bytendomods/RLCD-DMG/journey/img/IMG_0250 Large.jpeg

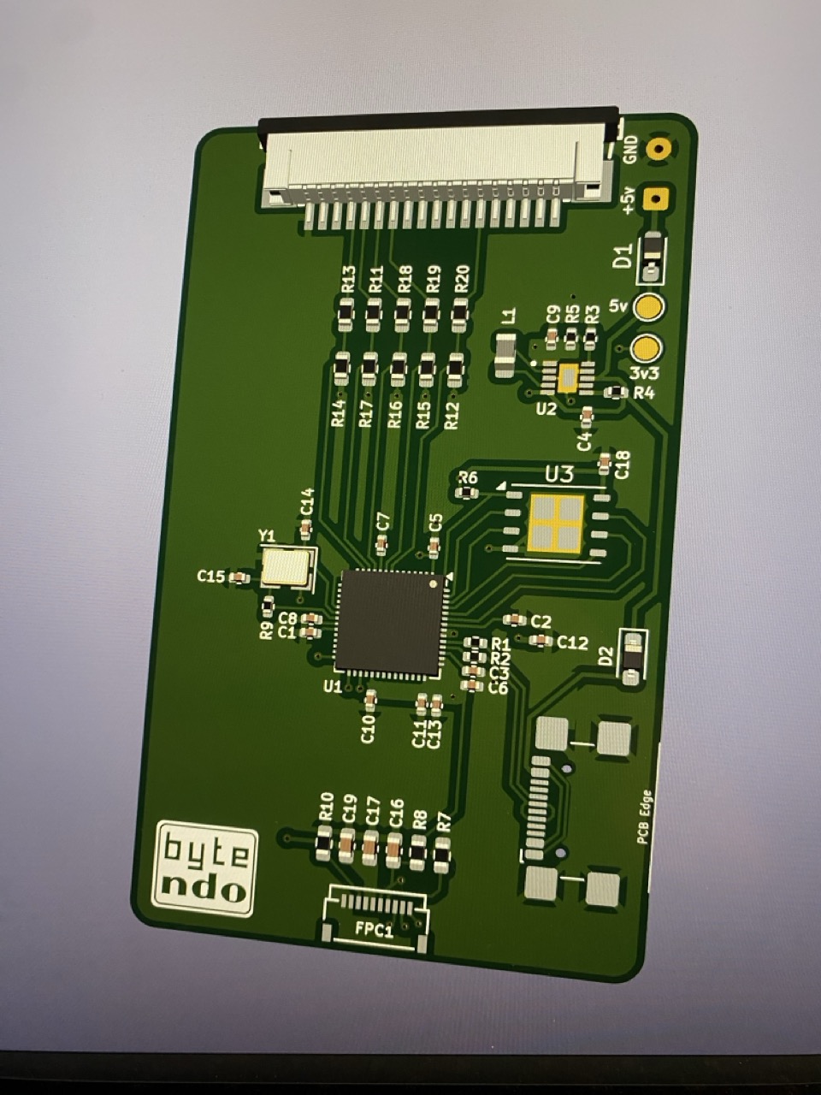
journey/img/IMG_0250 Large.jpeg
