bytendomods/RLCD-DMG/journey/img/IMG_0370 Large.jpeg

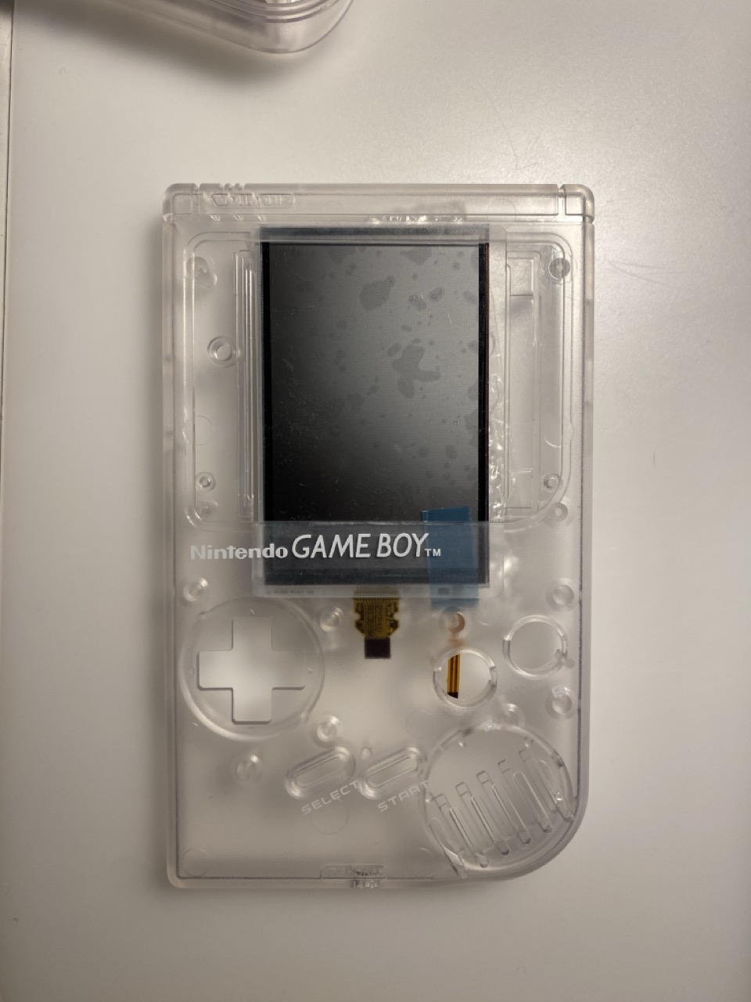
journey/img/IMG_0370 Large.jpeg
