bytendomods/RLCD-DMG/journey/img/IMG_0482 Large.jpeg

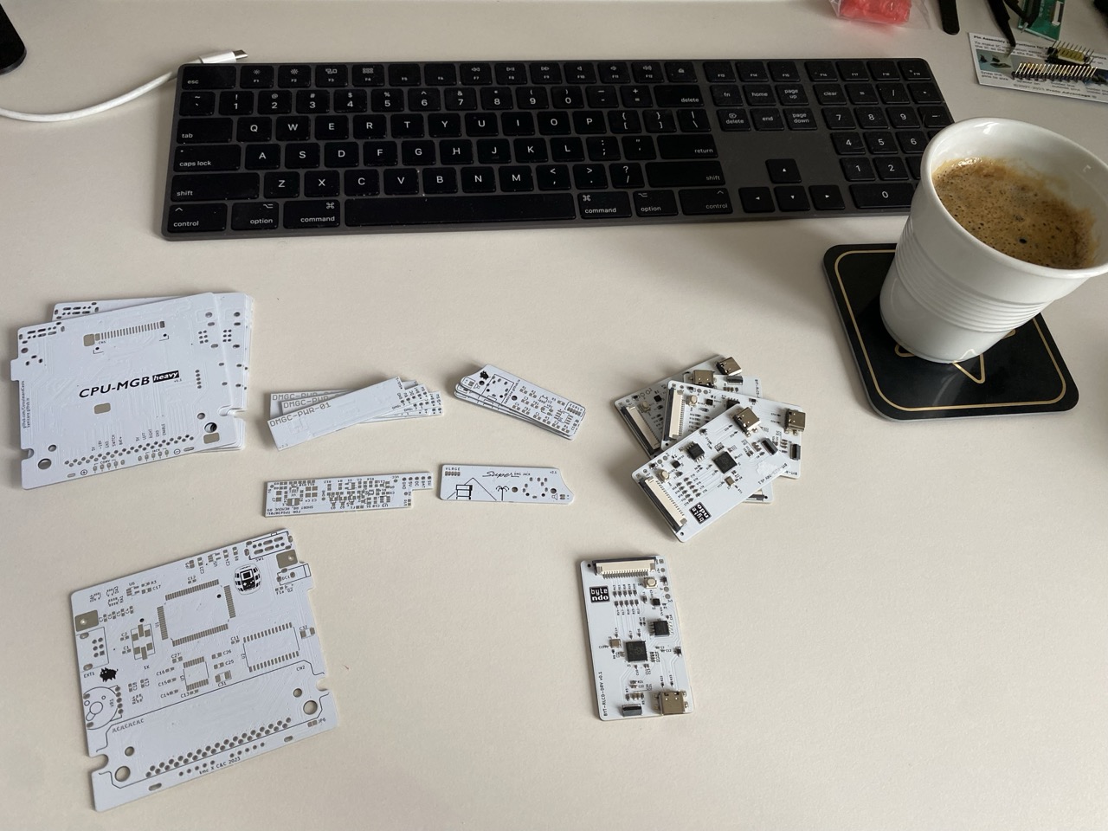
journey/img/IMG_0482 Large.jpeg
