bytendomods/RLCD-DMG/journey/img/IMG_0483 Large.jpeg

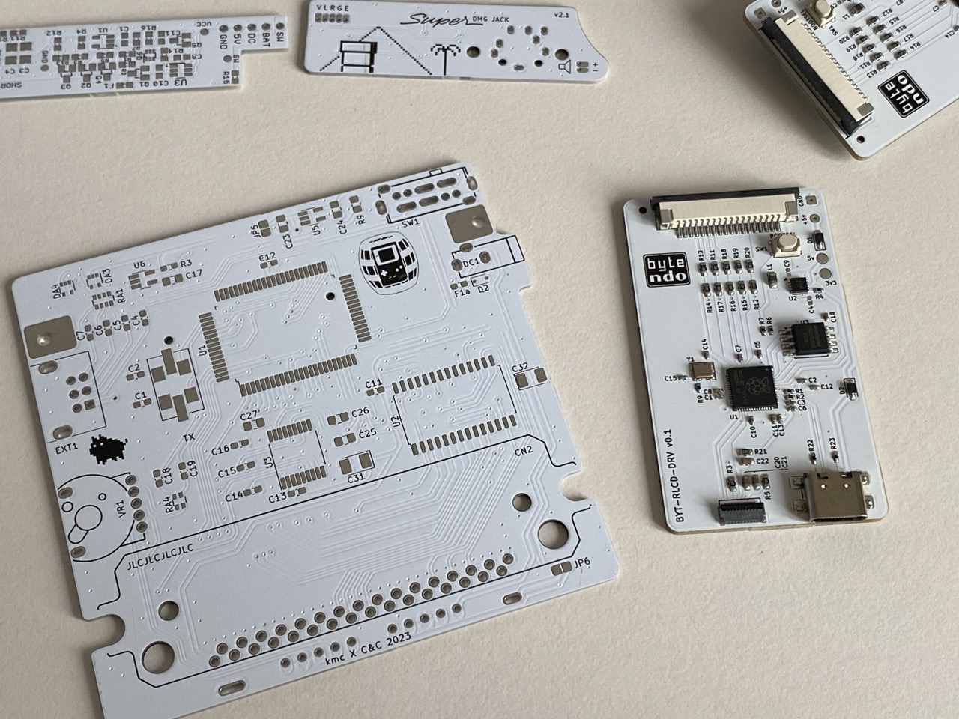
journey/img/IMG_0483 Large.jpeg
