bytendomods/RLCD-DMG/journey/img/IMG_0505 Large.jpeg

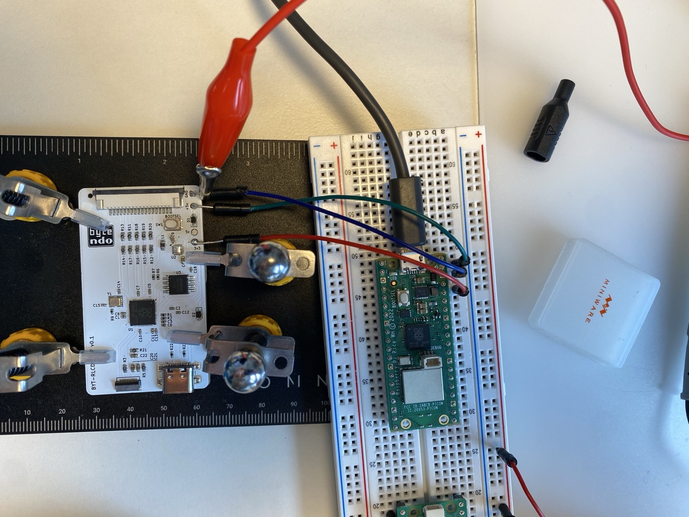
journey/img/IMG_0505 Large.jpeg
