bytendomods/RLCD-DMG/journey/img/IMG_0550 Large.jpeg

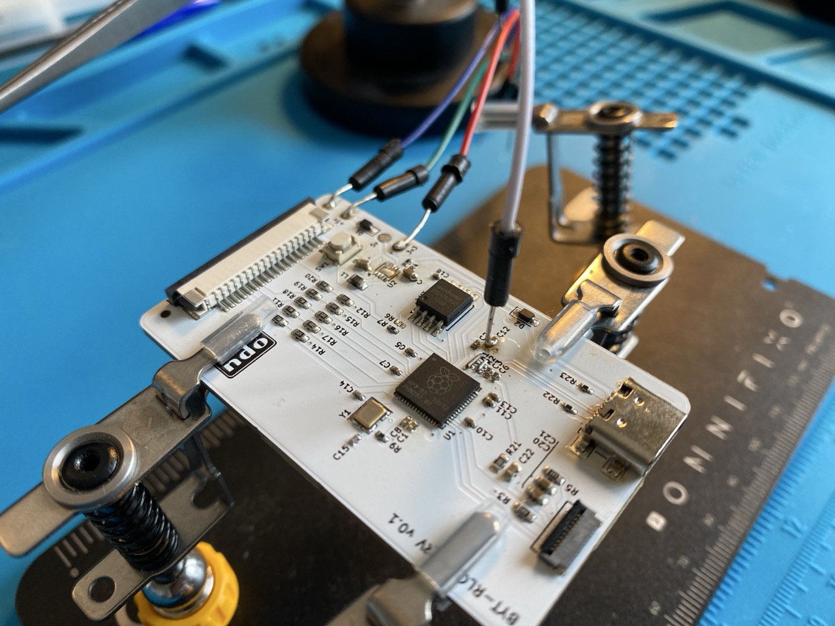
journey/img/IMG_0550 Large.jpeg
