bytendomods/RLCD-DMG/journey/img/IMG_0924 Large.jpeg

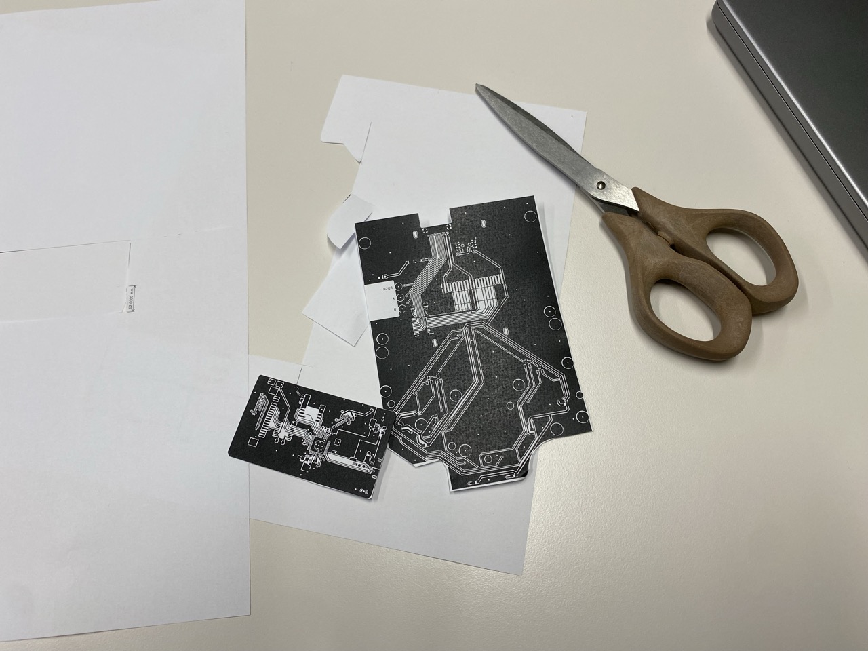
journey/img/IMG_0924 Large.jpeg
