bytendomods/RLCD-DMG/journey/img/IMG_0939 Large.jpeg

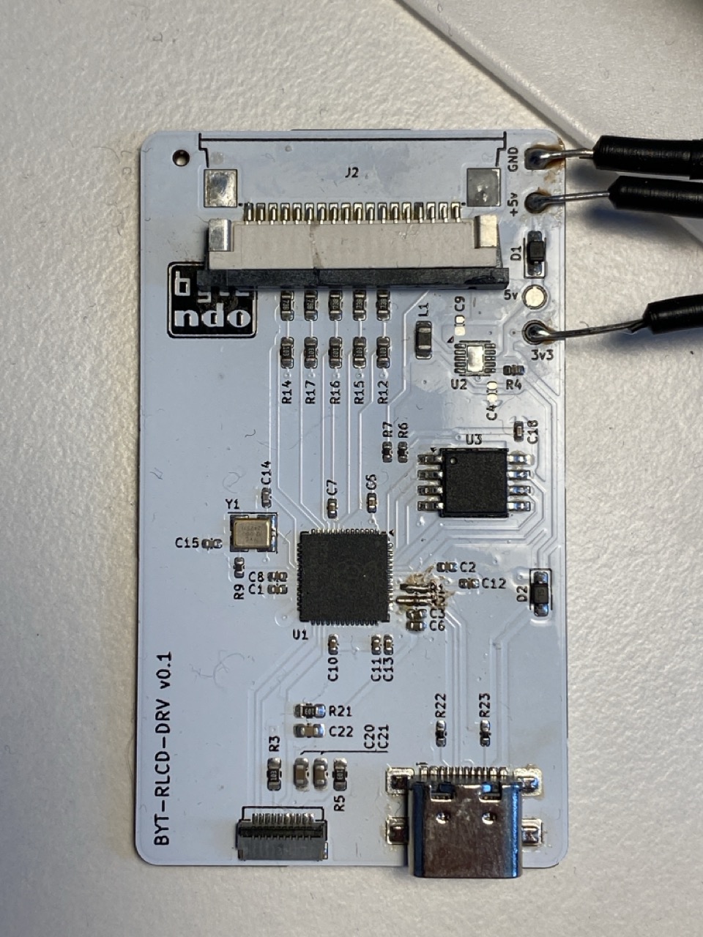
journey/img/IMG_0939 Large.jpeg
