bytendomods/RLCD-DMG/journey/img/IMG_4357 Large.jpeg

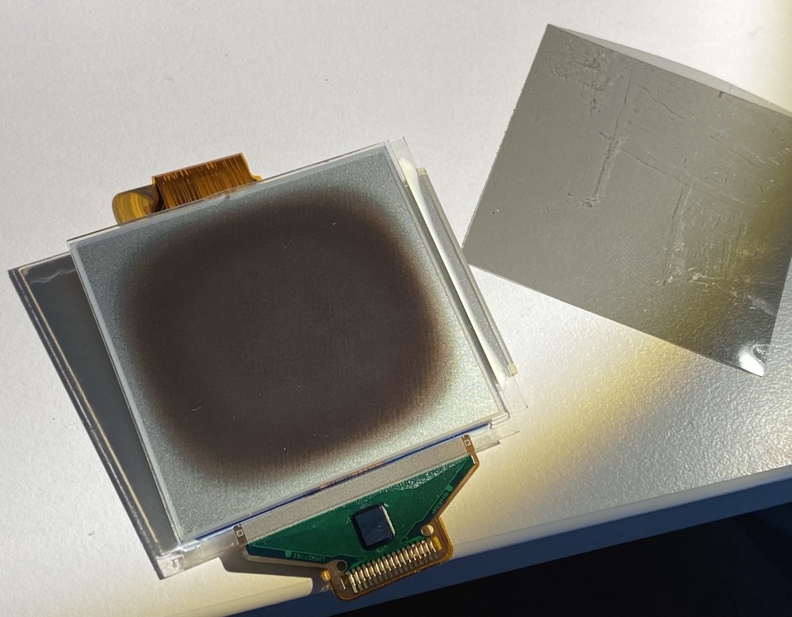
journey/img/IMG_4357 Large.jpeg
