bytendomods/RLCD-DMG/journey/img/IMG_4542 Large.jpeg

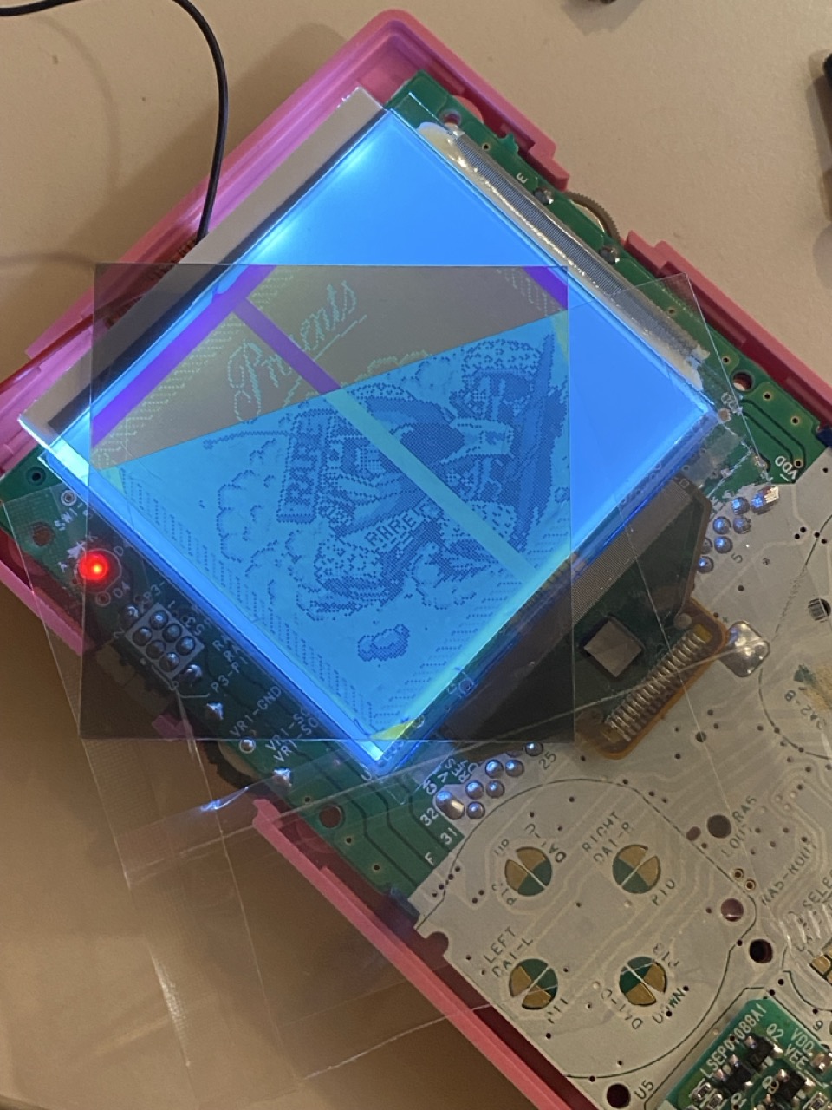
journey/img/IMG_4542 Large.jpeg
