bytendomods/RLCD-DMG/journey/img/IMG_4658 Large.jpeg

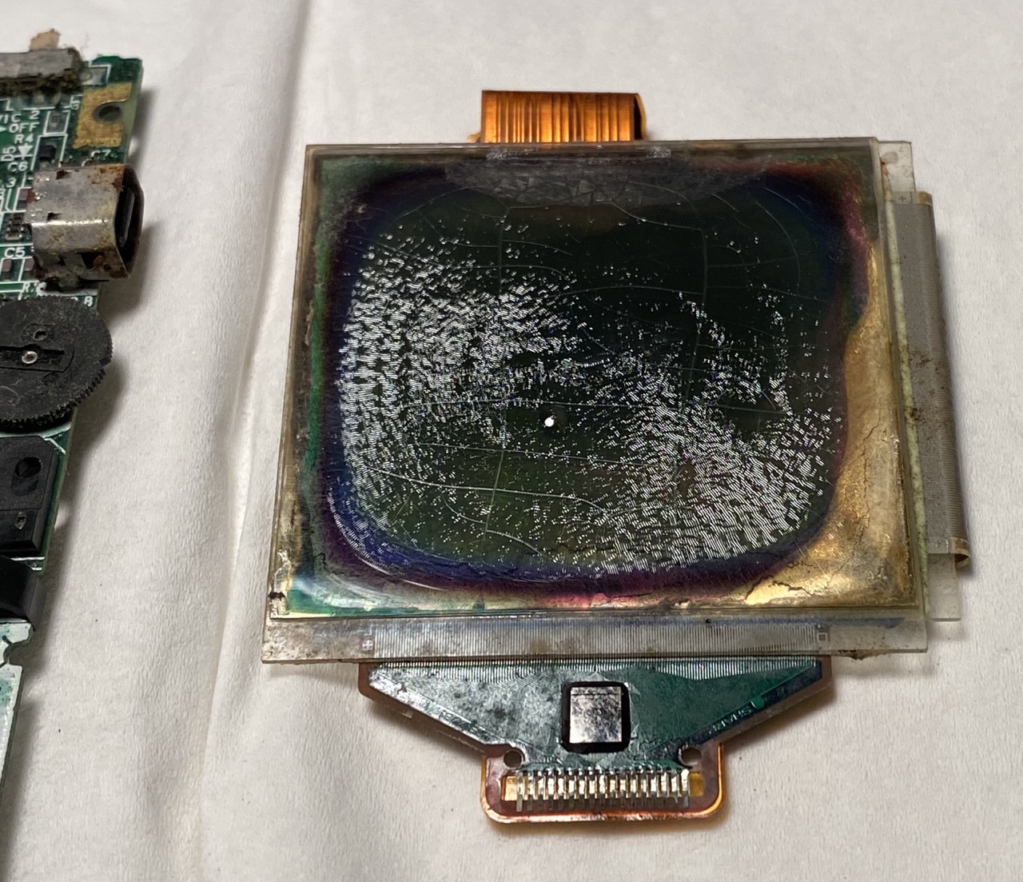
journey/img/IMG_4658 Large.jpeg
