bytendomods/RLCD-DMG/journey/img/IMG_6051 Large.jpeg

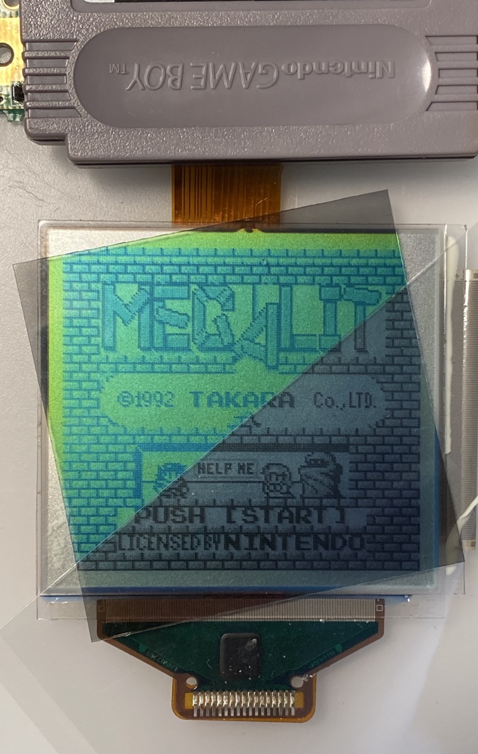
journey/img/IMG_6051 Large.jpeg
