bytendomods/RLCD-DMG/journey/img/IMG_6062 Large.jpeg

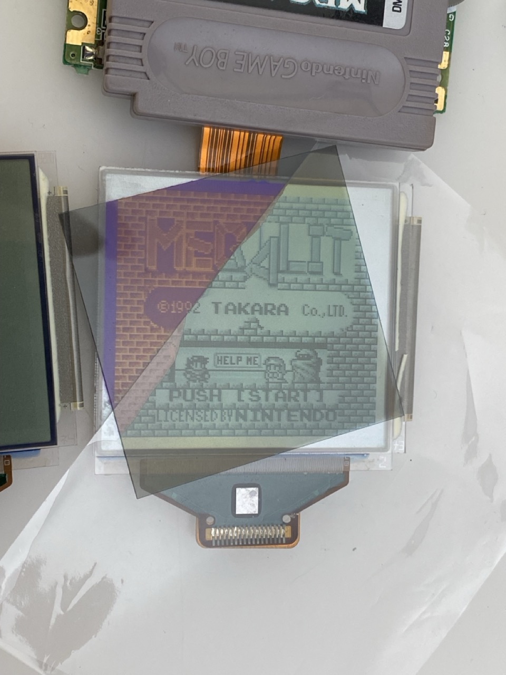
journey/img/IMG_6062 Large.jpeg
