bytendomods/RLCD-DMG/journey/img/IMG_6206 Large.jpeg

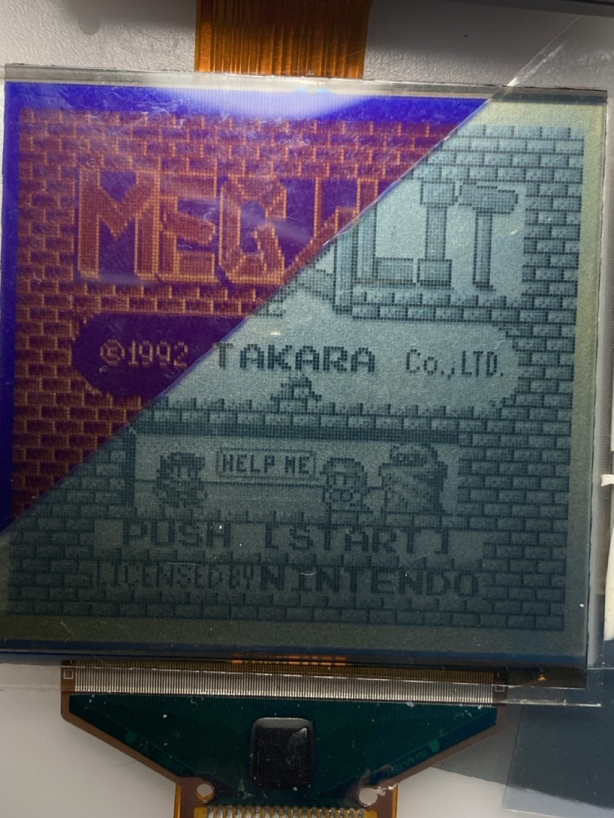
journey/img/IMG_6206 Large.jpeg
