bytendomods/RLCD-DMG/journey/img/IMG_6911 Large.jpeg

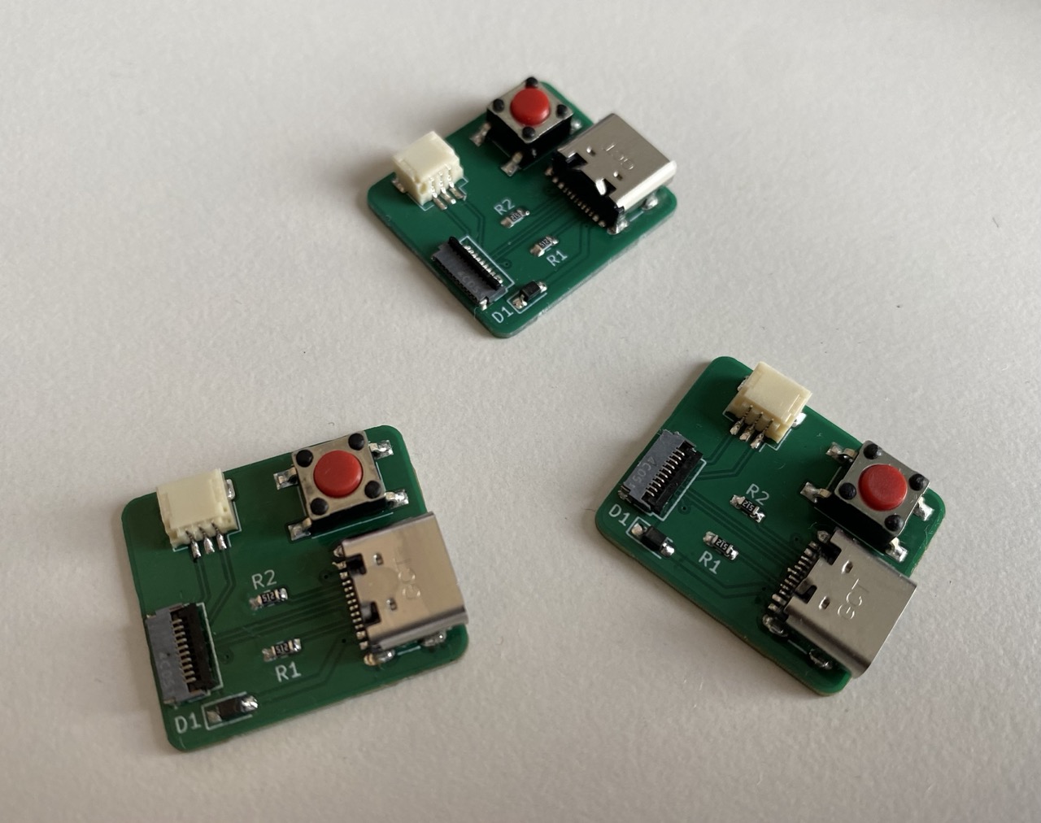
journey/img/IMG_6911 Large.jpeg
