bytendomods/RLCD-DMG/journey/img/IMG_6912 Large.jpeg

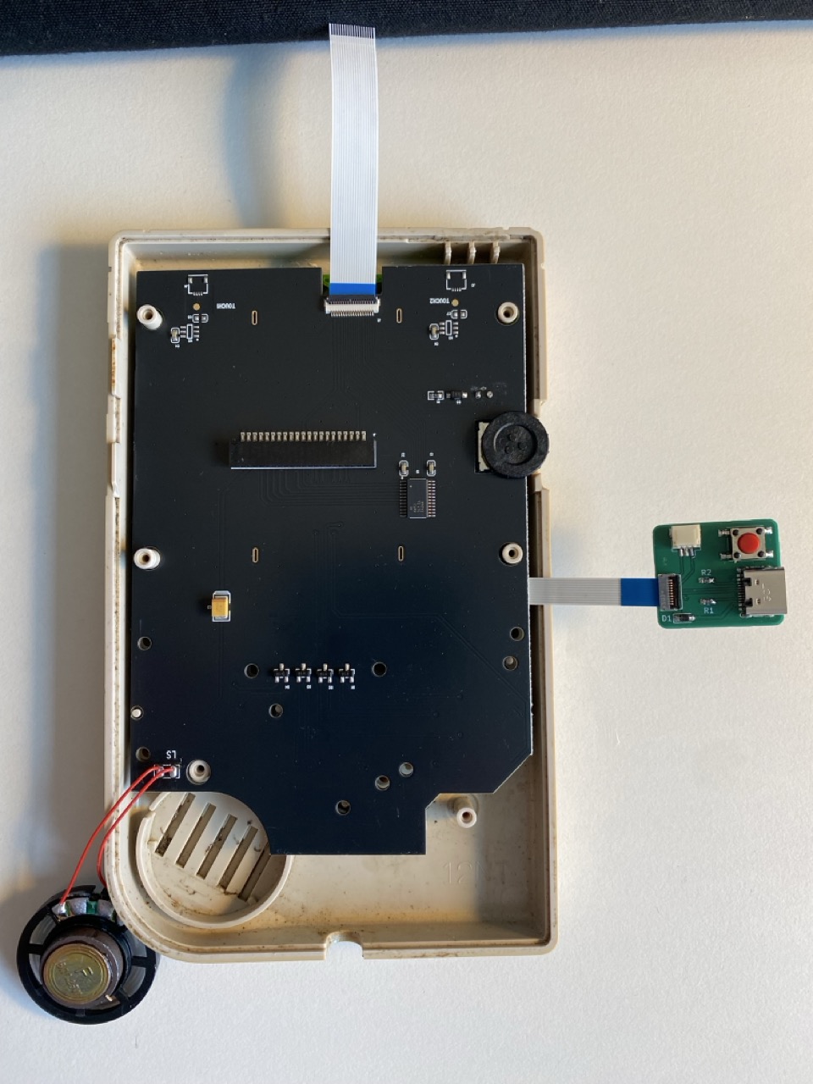
journey/img/IMG_6912 Large.jpeg
