bytendomods/RLCD-DMG/journey/img/IMG_6913 Large.jpeg

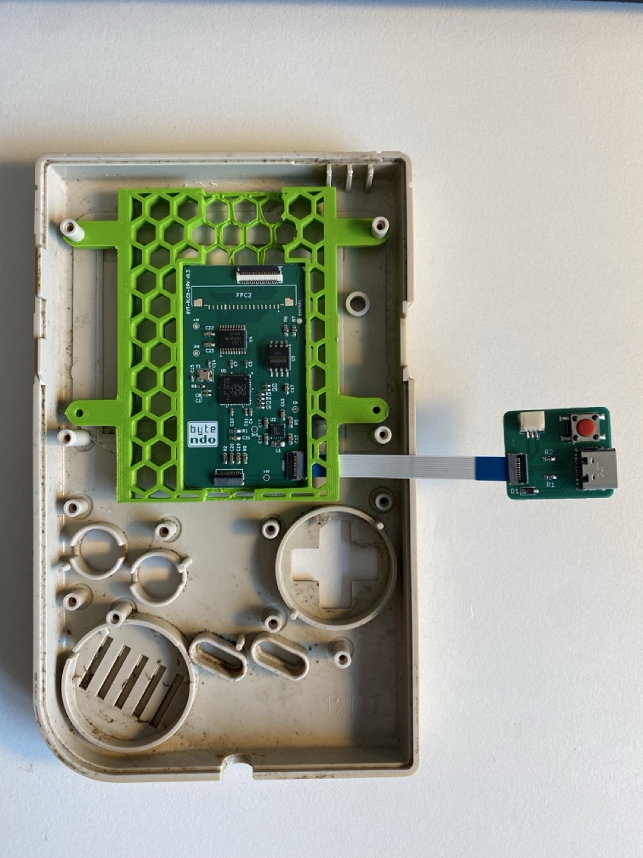
journey/img/IMG_6913 Large.jpeg
