bytendomods/RLCD-DMG/journey/img/IMG_7461 Large.jpeg

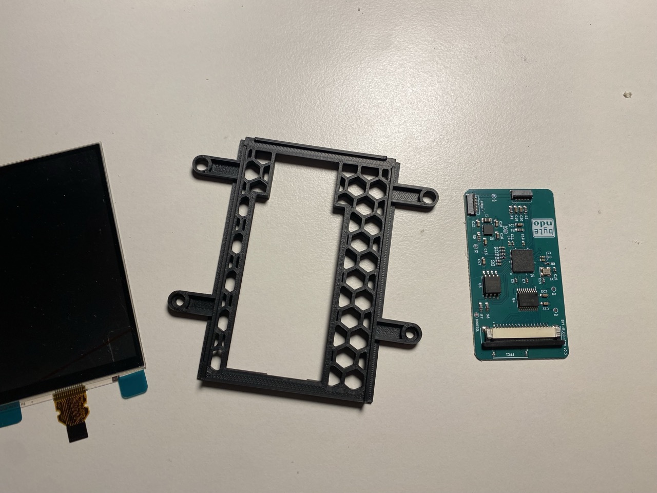
journey/img/IMG_7461 Large.jpeg
