bytendomods/RLCD-DMG/journey/img/IMG_7461(1) Large.jpeg

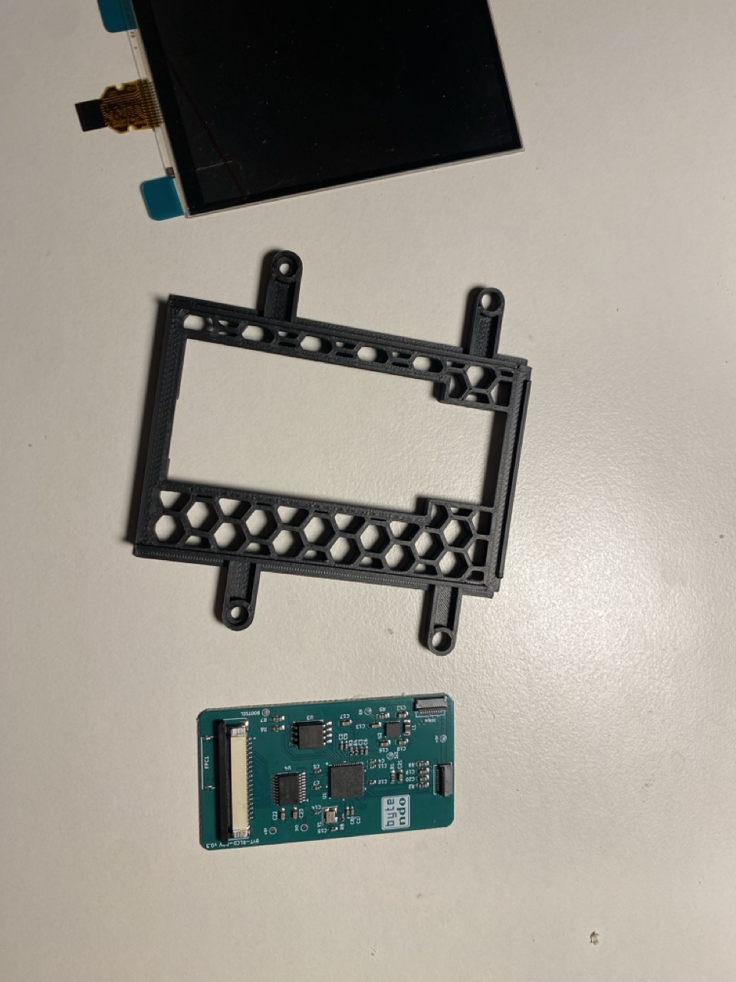
journey/img/IMG_7461(1) Large.jpeg
