bytendomods/RLCD-DMG/journey/img/IMG_7463 Large.jpeg

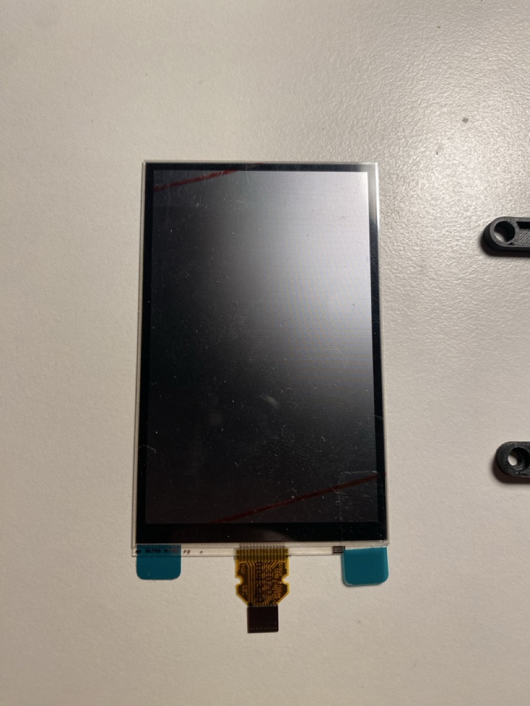
journey/img/IMG_7463 Large.jpeg
