bytendomods/RLCD-DMG/journey/img/IMG_7464 Large.jpeg

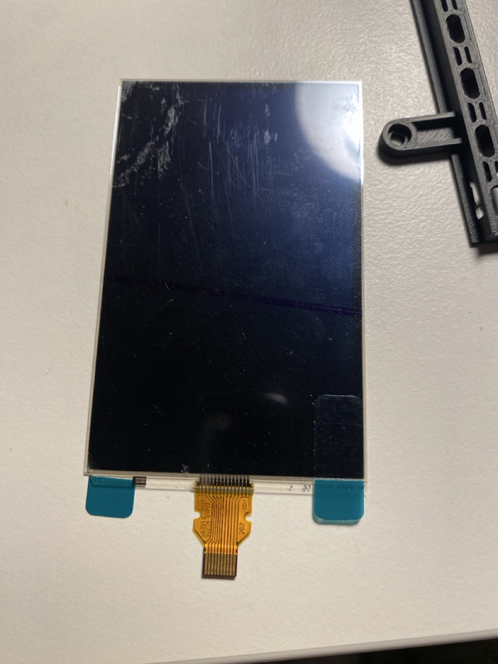
journey/img/IMG_7464 Large.jpeg
