bytendomods/RLCD-DMG/journey/img/IMG_7466 Large.jpeg

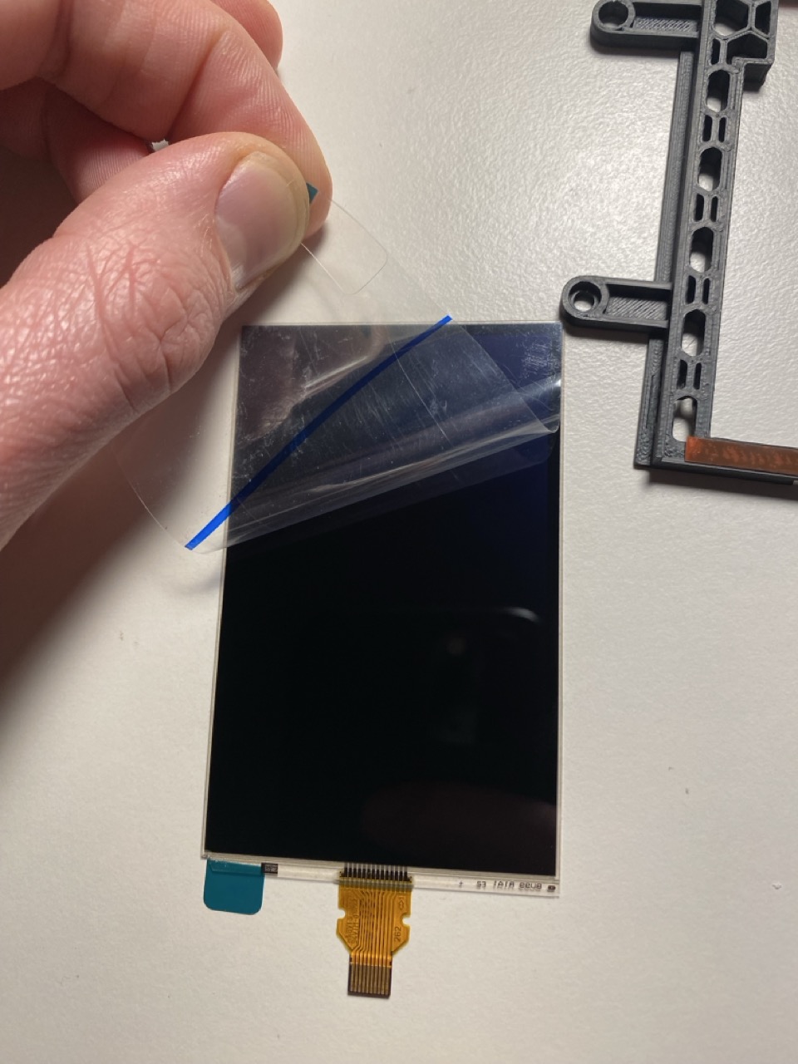
journey/img/IMG_7466 Large.jpeg
