bytendomods/RLCD-DMG/journey/img/IMG_7468(1) Large.jpeg

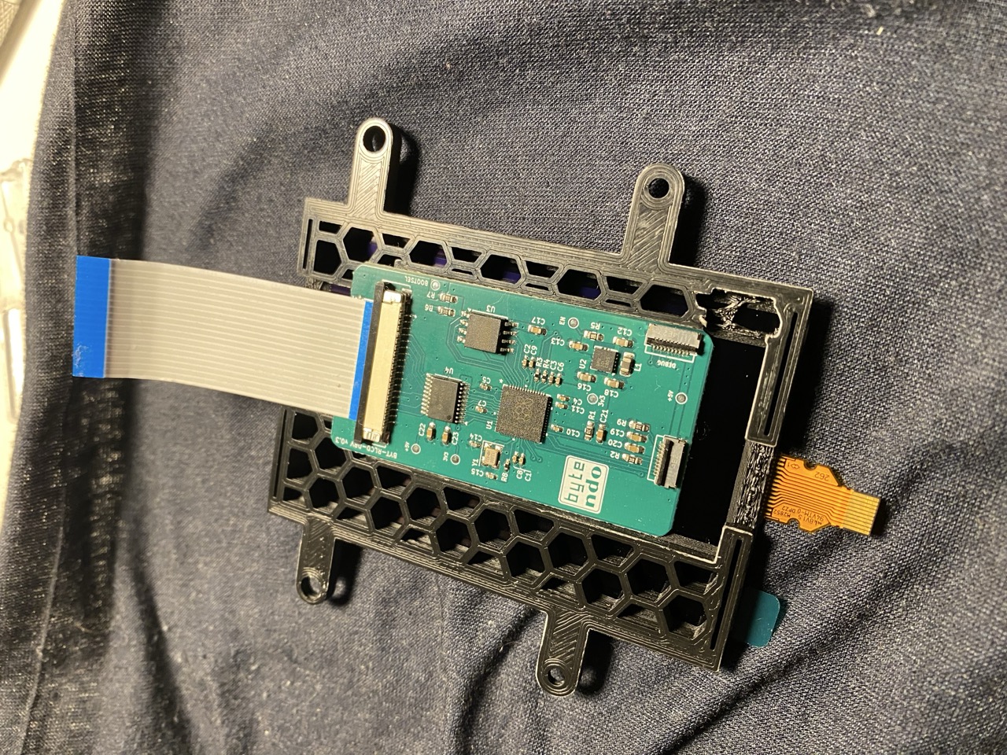
journey/img/IMG_7468(1) Large.jpeg
