bytendomods/RLCD-DMG/journey/img/IMG_7469 Large.jpeg

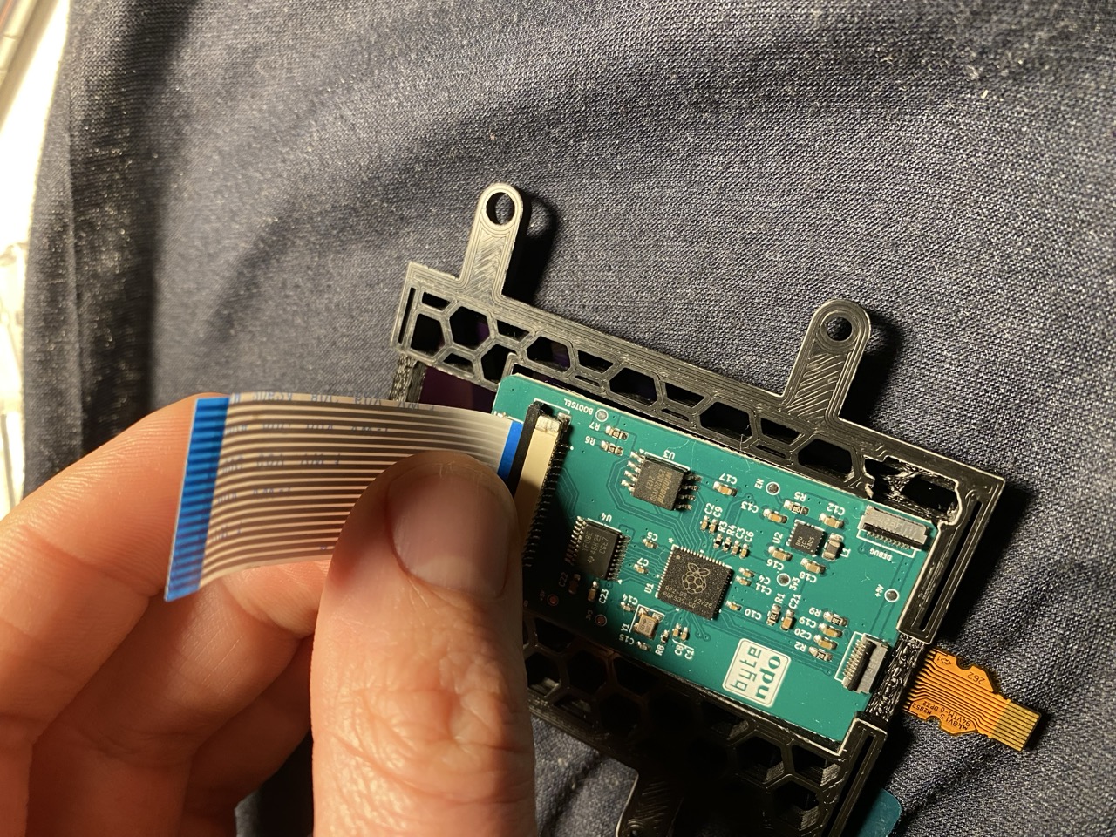
journey/img/IMG_7469 Large.jpeg
