bytendomods/RLCD-DMG/journey/img/IMG_7469(1) Large.jpeg

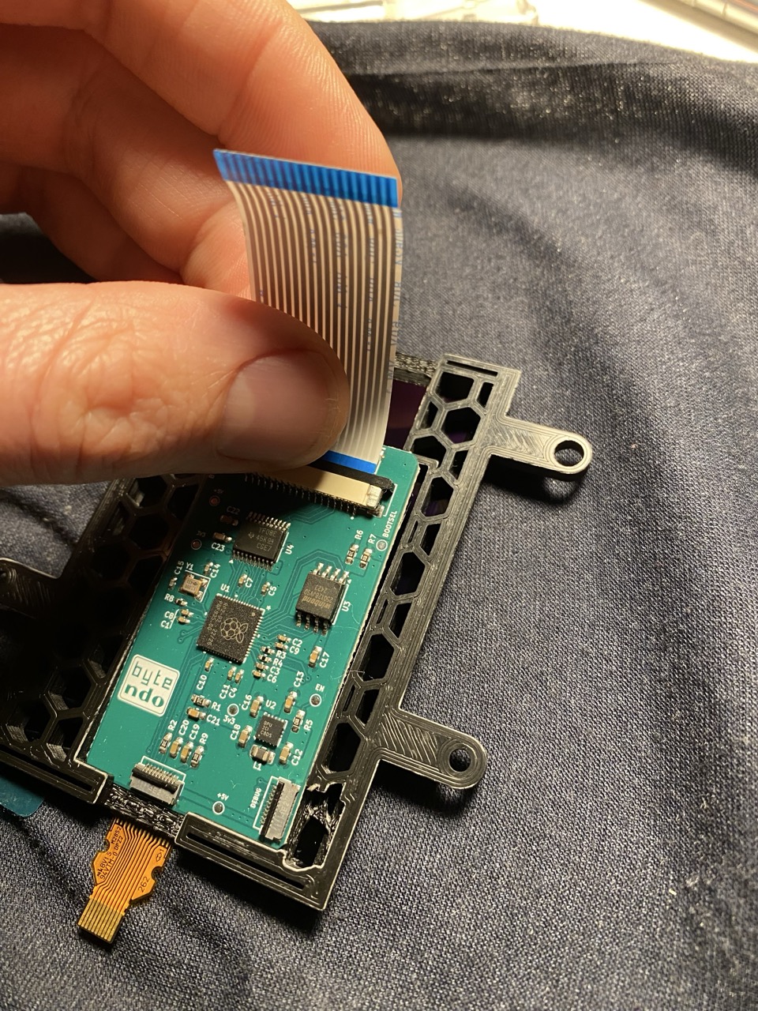
journey/img/IMG_7469(1) Large.jpeg
