bytendomods/RLCD-DMG/journey/img/IMG_7470(1) Large.jpeg

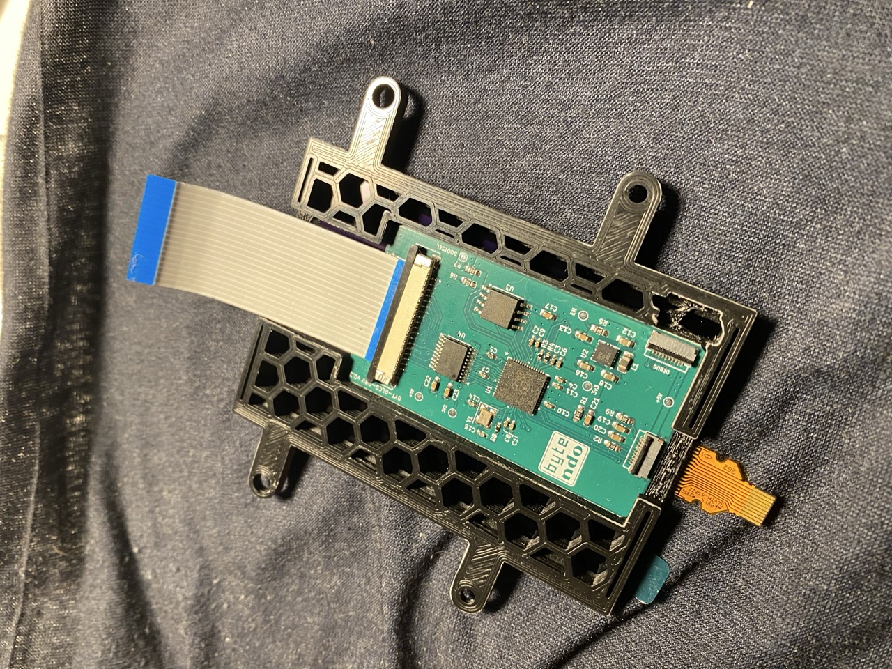
journey/img/IMG_7470(1) Large.jpeg
