bytendomods/RLCD-DMG/journey/img/IMG_7471(1) Large.jpeg

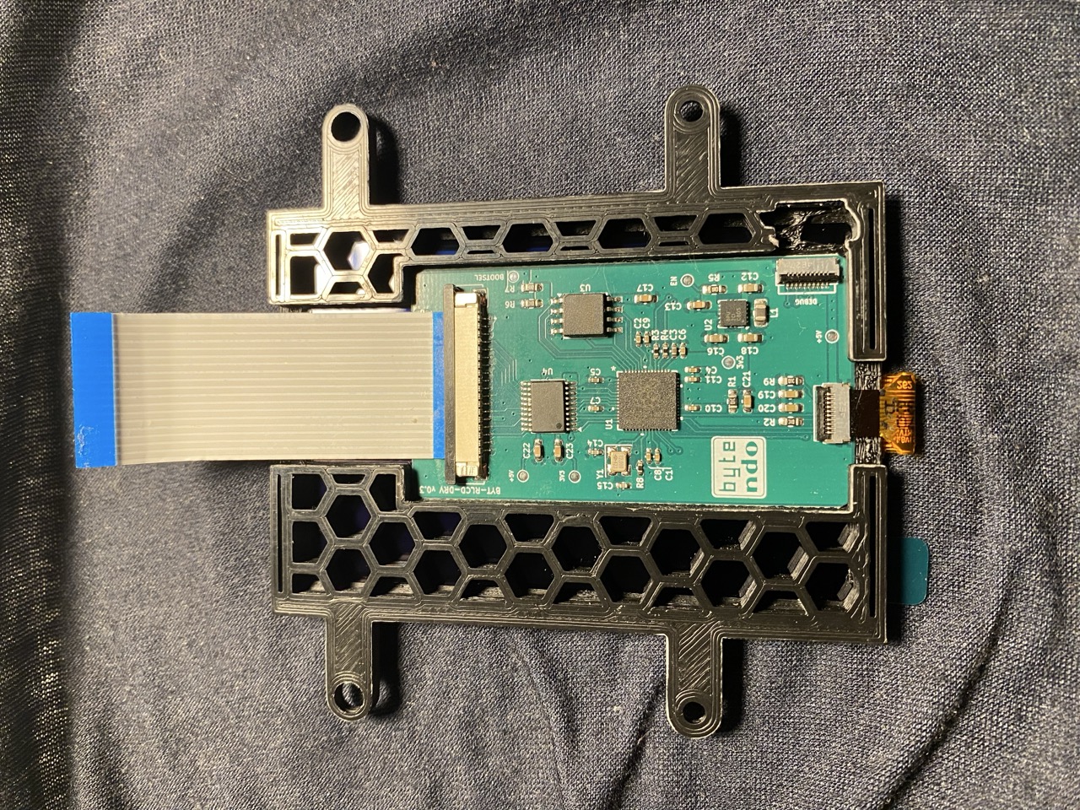
journey/img/IMG_7471(1) Large.jpeg
