bytendomods/RLCD-DMG/journey/img/IMG_7472(1) Large.jpeg

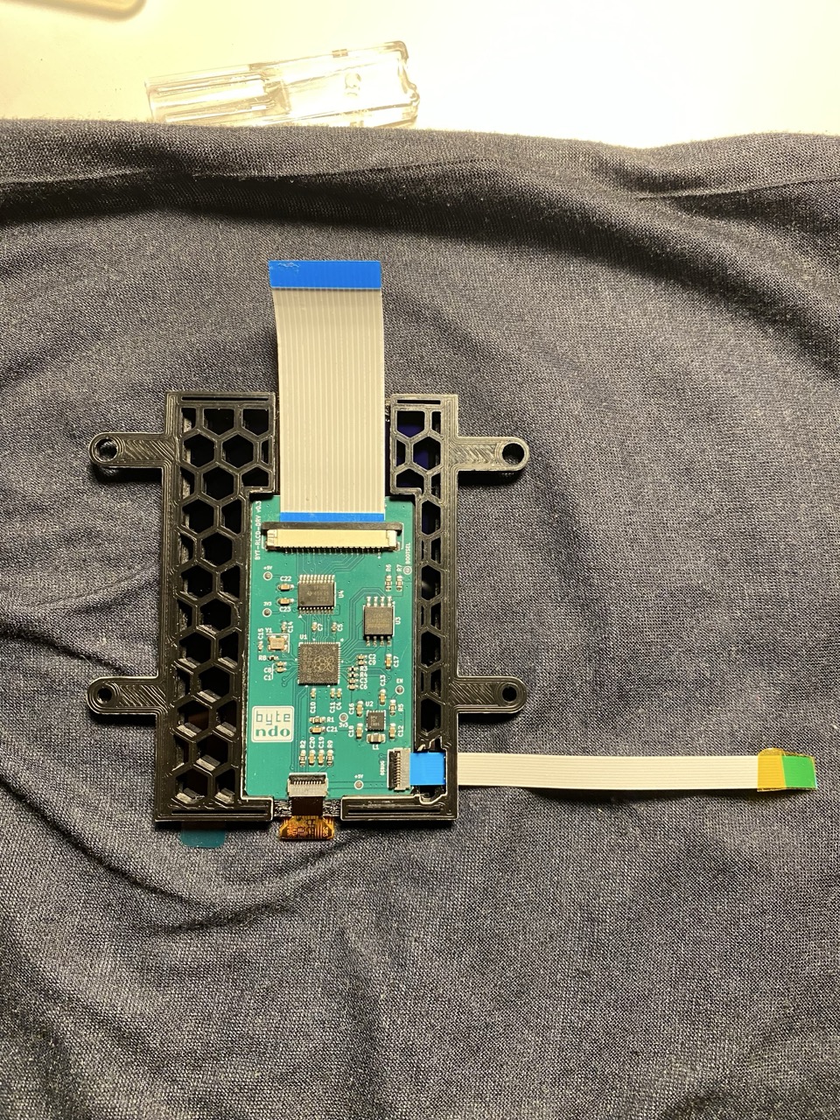
journey/img/IMG_7472(1) Large.jpeg
