bytendomods/RLCD-DMG/journey/img/IMG_7578 Large.jpeg

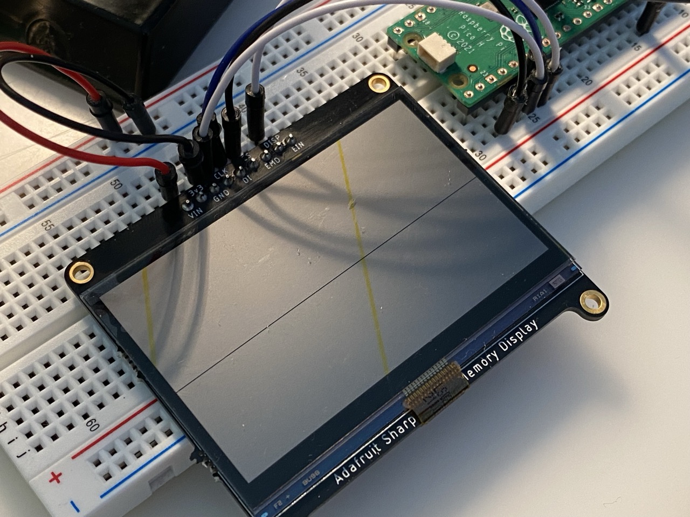
journey/img/IMG_7578 Large.jpeg
