bytendomods/RLCD-DMG/journey/img/IMG_7606 Large.jpeg

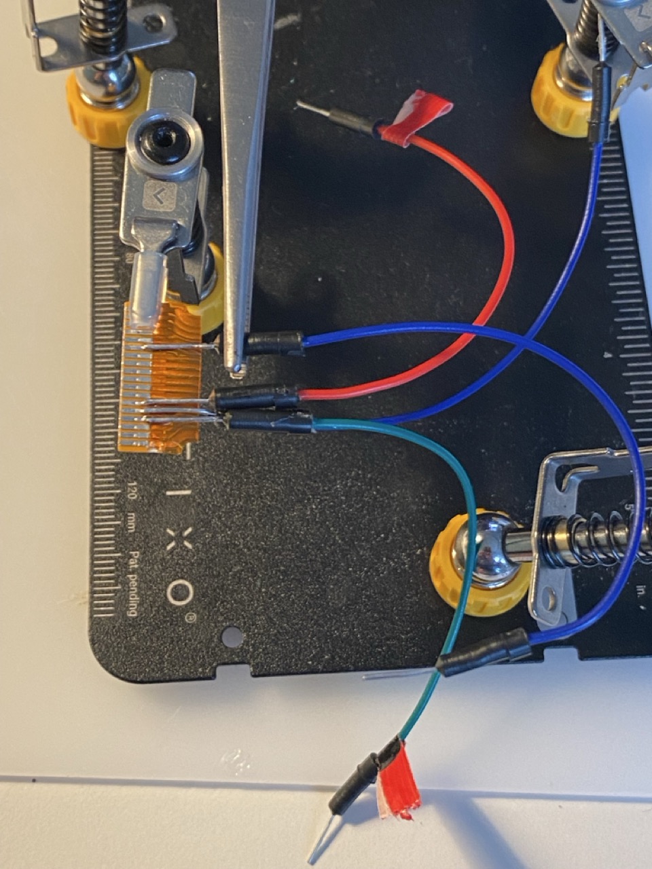
journey/img/IMG_7606 Large.jpeg
