bytendomods/RLCD-DMG/journey/img/IMG_7609 Large.jpeg

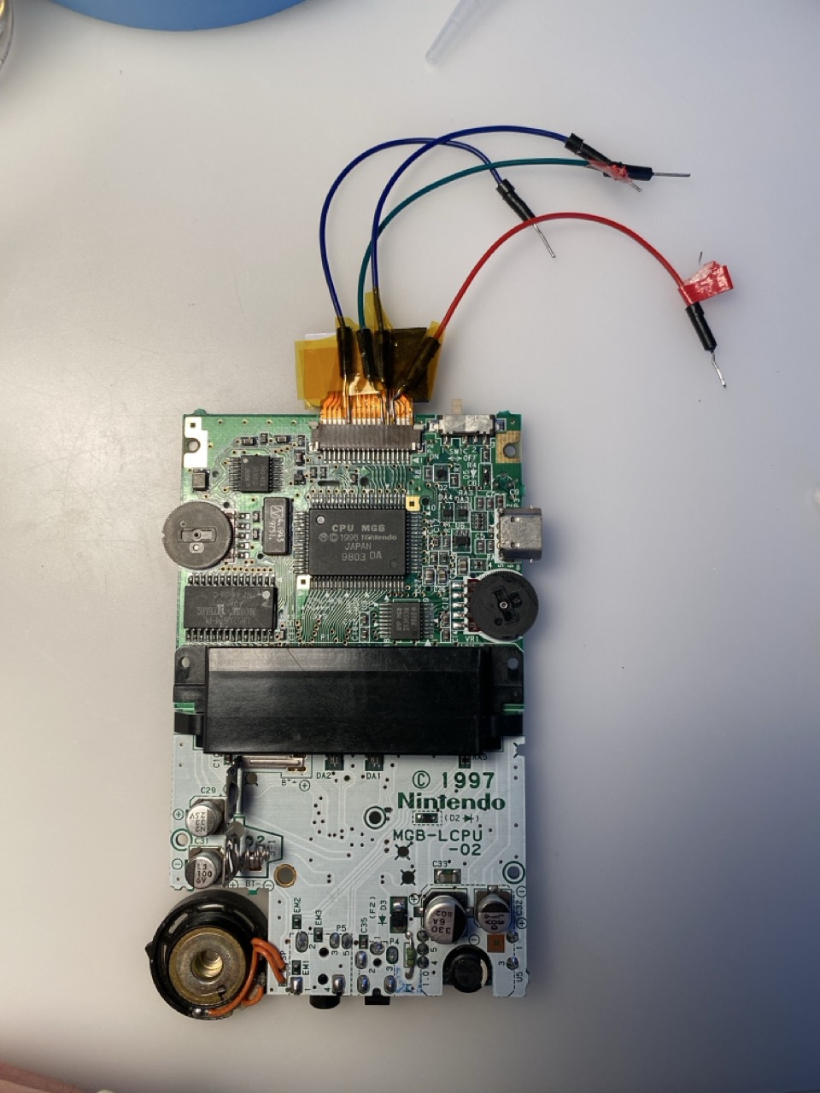
journey/img/IMG_7609 Large.jpeg
