bytendomods/RLCD-DMG/journey/img/IMG_7625 Large.jpeg

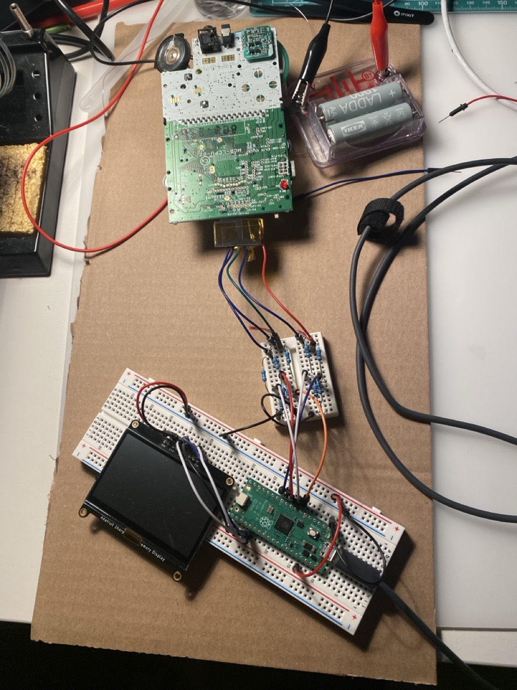
journey/img/IMG_7625 Large.jpeg
