bytendomods/RLCD-DMG/journey/img/IMG_7663 Large.jpeg

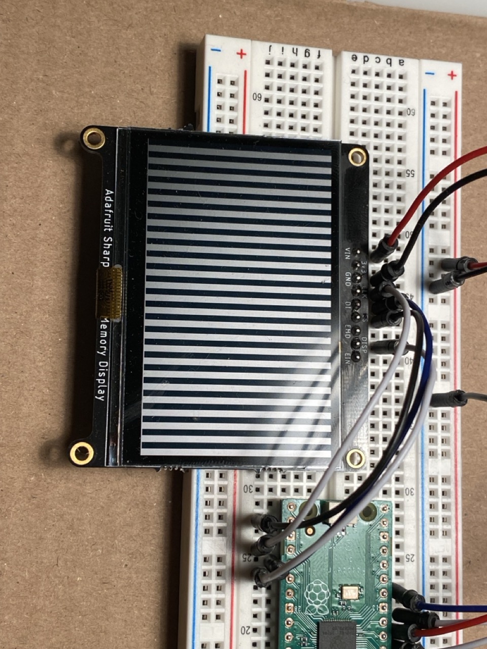
journey/img/IMG_7663 Large.jpeg
