bytendomods/RLCD-DMG/journey/img/IMG_7675 Large.jpeg

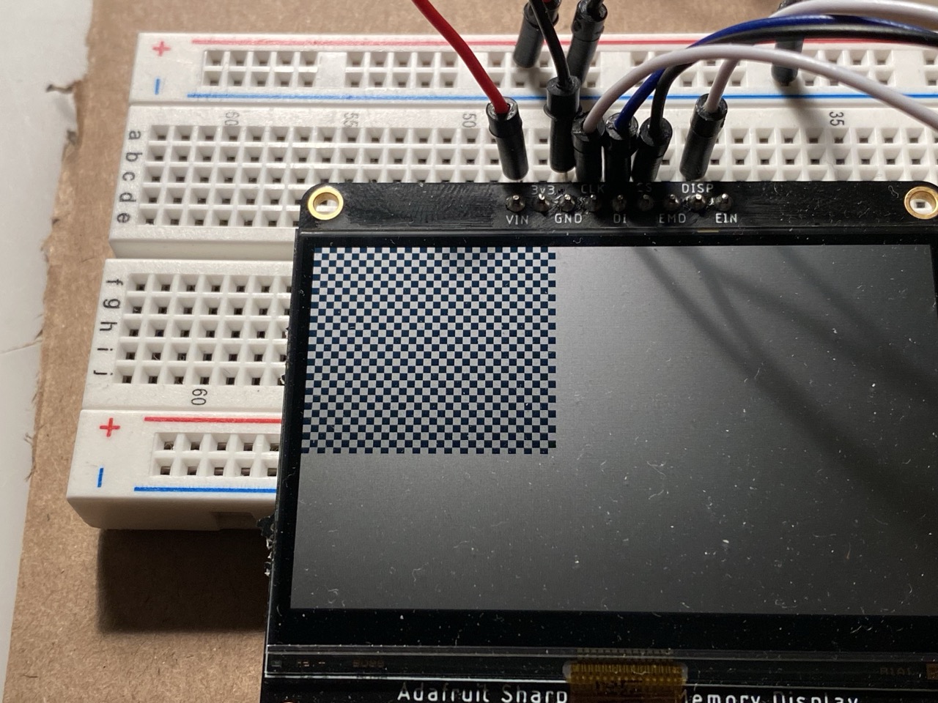
journey/img/IMG_7675 Large.jpeg
