bytendomods/RLCD-DMG/journey/img/IMG_7688 Large.jpeg

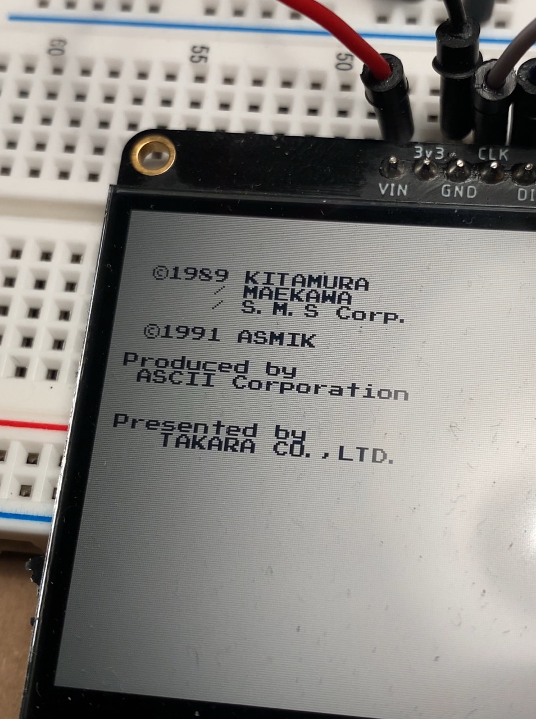
journey/img/IMG_7688 Large.jpeg
