bytendomods/RLCD-DMG/journey/img/IMG_7689 Large.jpeg

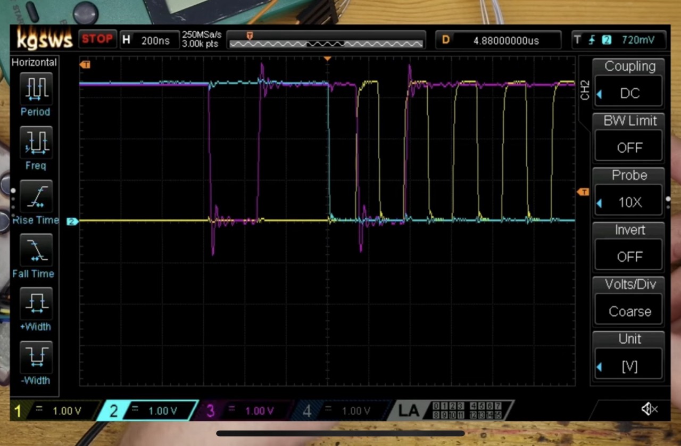
journey/img/IMG_7689 Large.jpeg
