bytendomods/RLCD-DMG/journey/img/IMG_8142 Large.jpeg

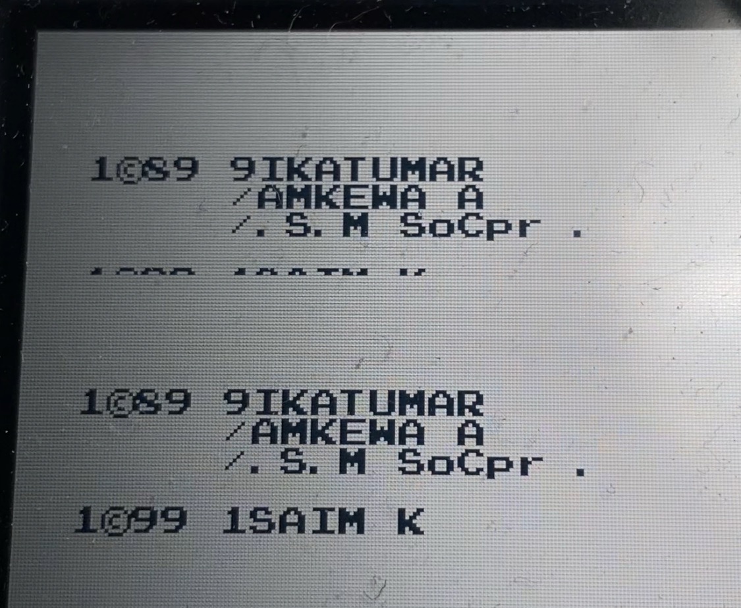
journey/img/IMG_8142 Large.jpeg
