bytendomods/RLCD-DMG/journey/img/IMG_9238 Large.jpeg

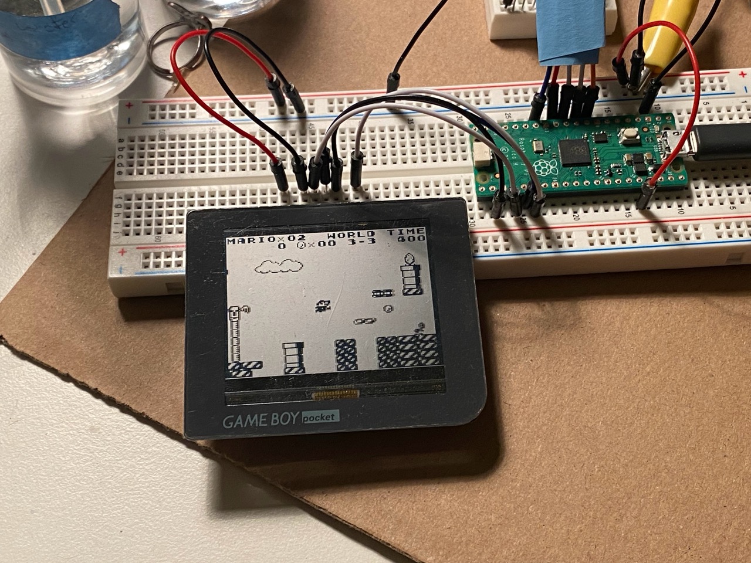
journey/img/IMG_9238 Large.jpeg
