bytendomods/RLCD-DMG/journey/img/IMG_9249 Large.jpeg

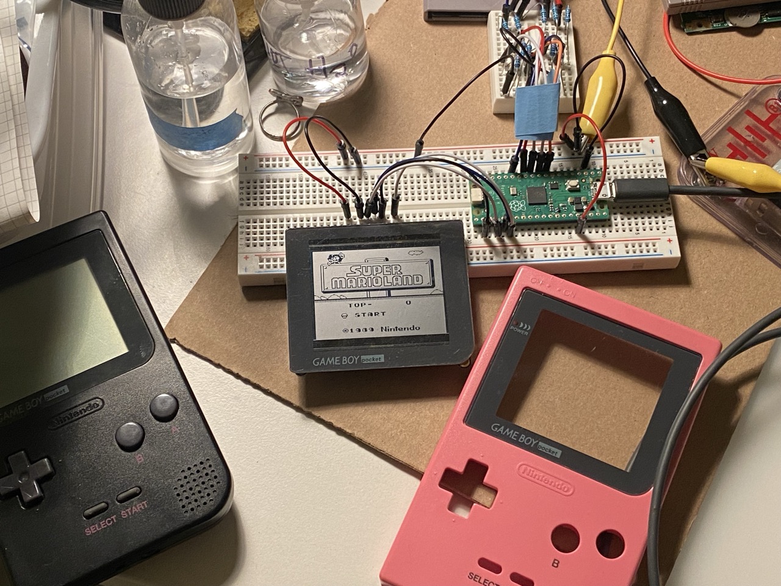
journey/img/IMG_9249 Large.jpeg
