bytendomods/RLCD-DMG/journey/img/IMG_9285 Large.jpeg

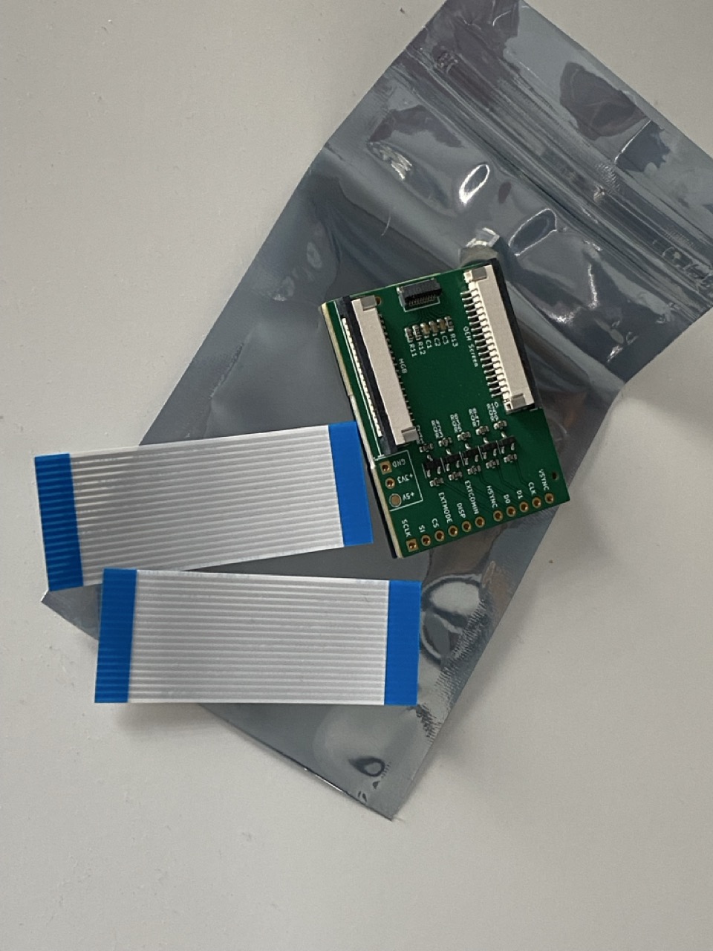
journey/img/IMG_9285 Large.jpeg
