bytendomods/RLCD-DMG/journey/img/IMG_9297 Large.jpeg

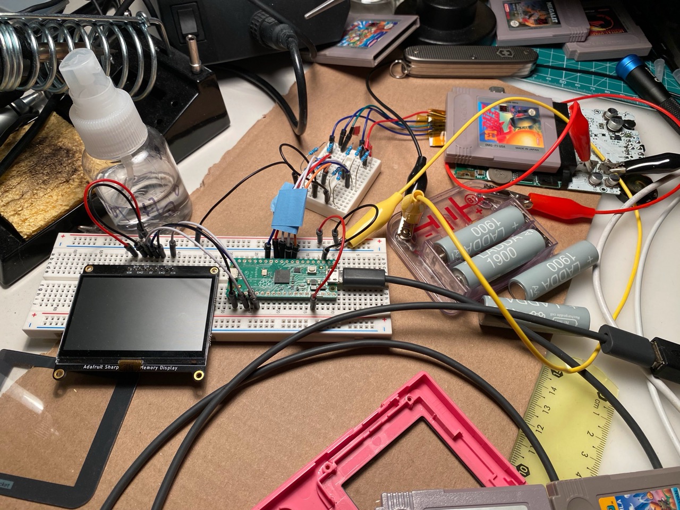
journey/img/IMG_9297 Large.jpeg
