bytendomods/RLCD-DMG/journey/img/IMG_9397 Large.jpeg

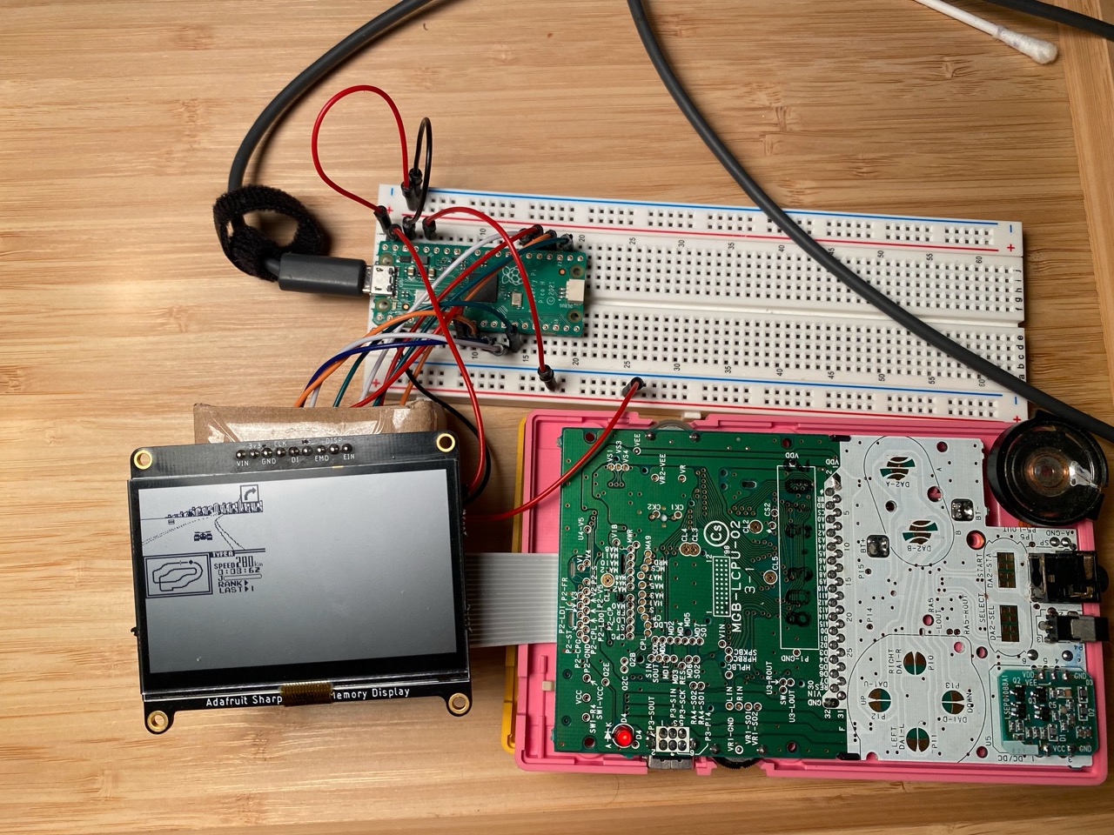
journey/img/IMG_9397 Large.jpeg
