bytendomods/RLCD-DMG/journey/img/IMG_9464 Large.jpeg

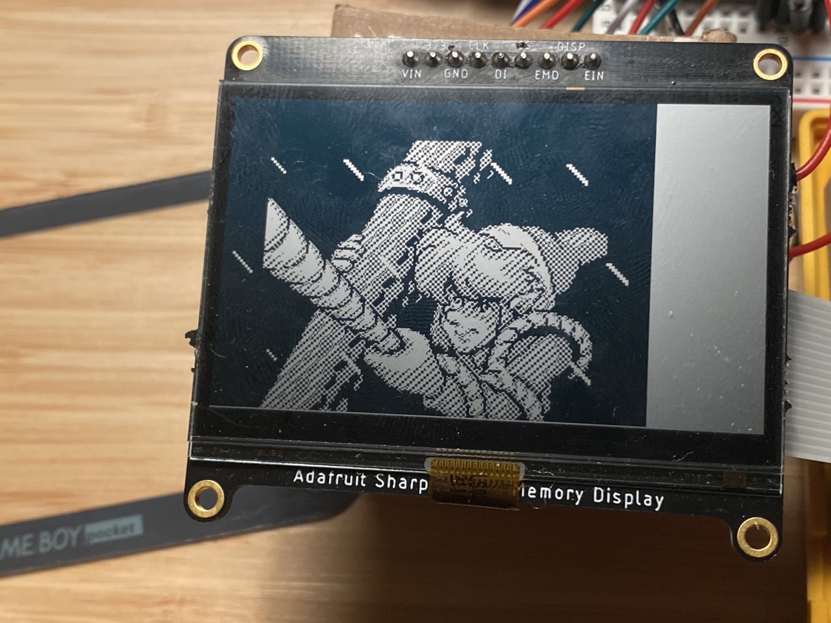
journey/img/IMG_9464 Large.jpeg
