bytendomods/RLCD-DMG/journey/img/IMG_9466 Large.jpeg

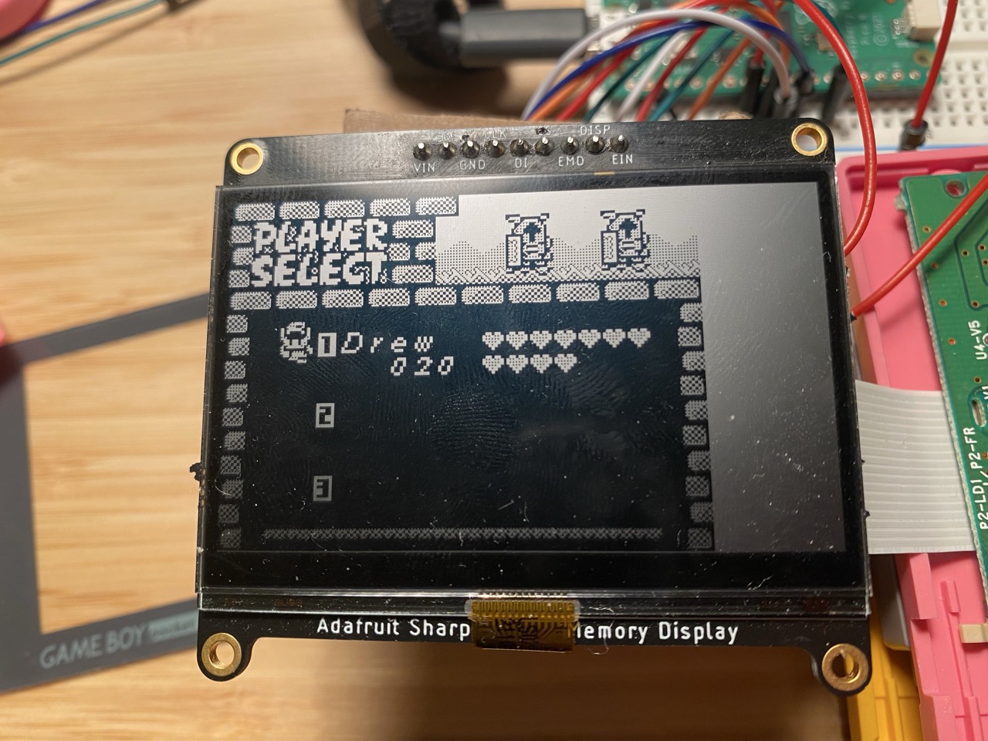
journey/img/IMG_9466 Large.jpeg
