bytendomods/RLCD-DMG/journey/img/IMG_9599 Large.jpeg

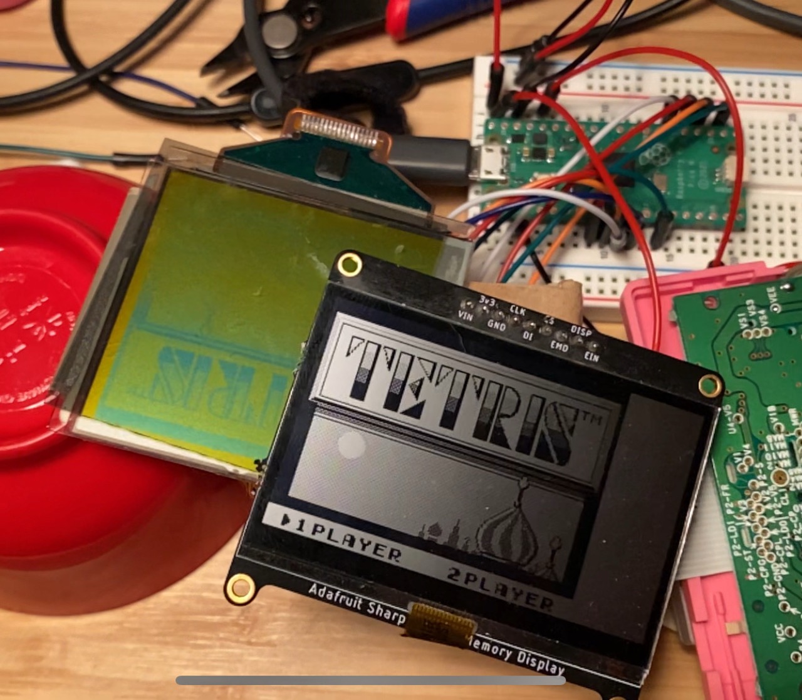
journey/img/IMG_9599 Large.jpeg
