bytendomods/RLCD-DMG/journey/img/IMG_9602 Large.jpeg

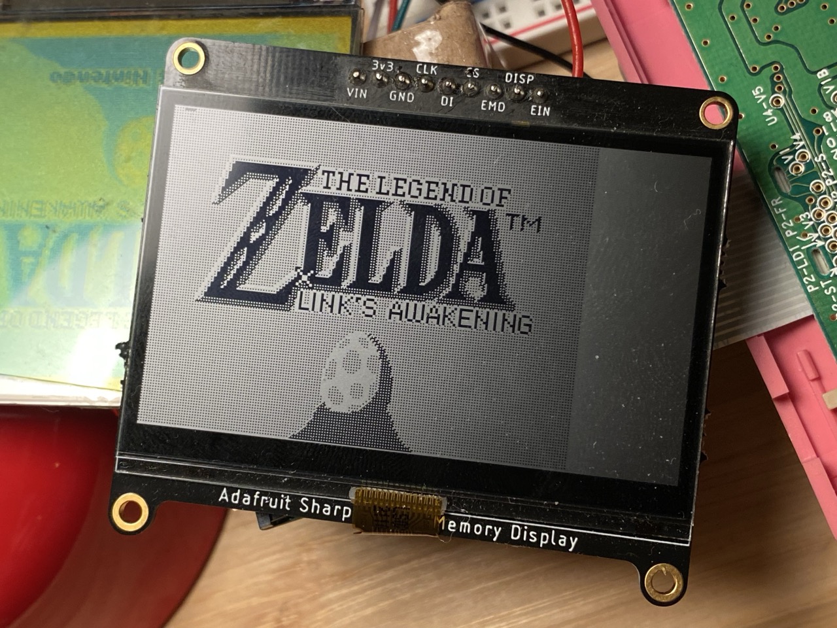
journey/img/IMG_9602 Large.jpeg
