bytendomods/RLCD-DMG/journey/img/IMG_9606 Large.jpeg

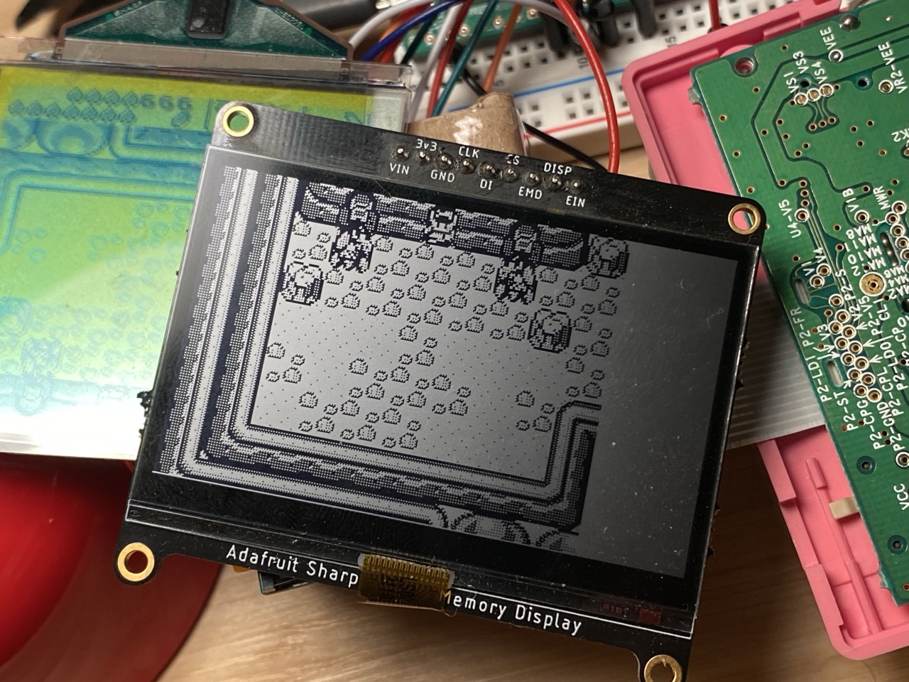
journey/img/IMG_9606 Large.jpeg
