bytendomods/RLCD-DMG/journey/img/IMG_9608 Large.jpeg

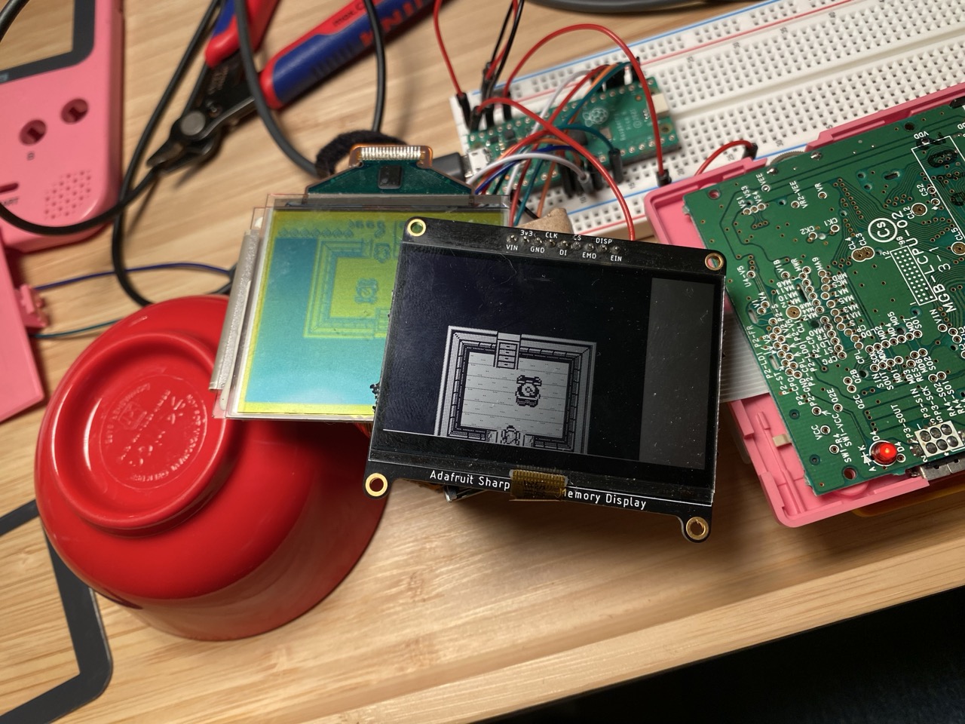
journey/img/IMG_9608 Large.jpeg
