bytendomods/RLCD-DMG/journey/img/IMG_9644 Large.jpeg

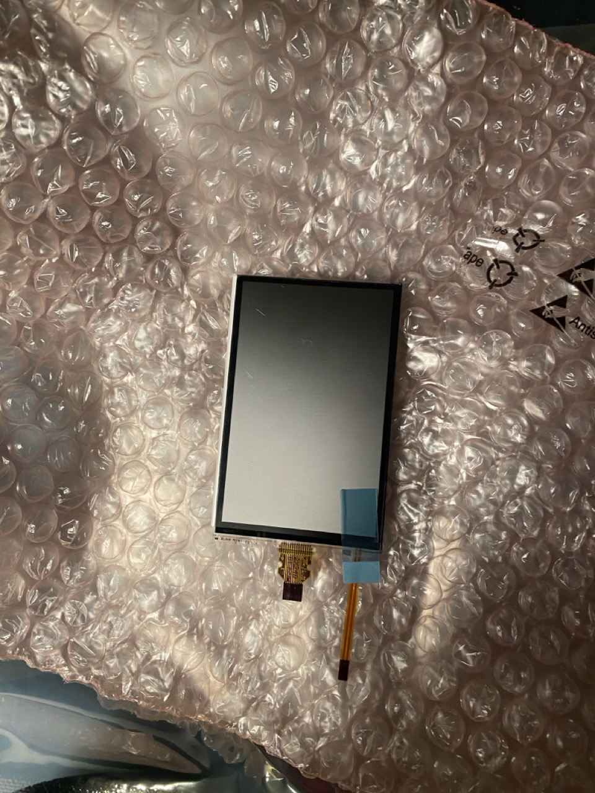
journey/img/IMG_9644 Large.jpeg
