bytendomods/RLCD-DMG/journey/img/IMG_9645 Large.jpeg

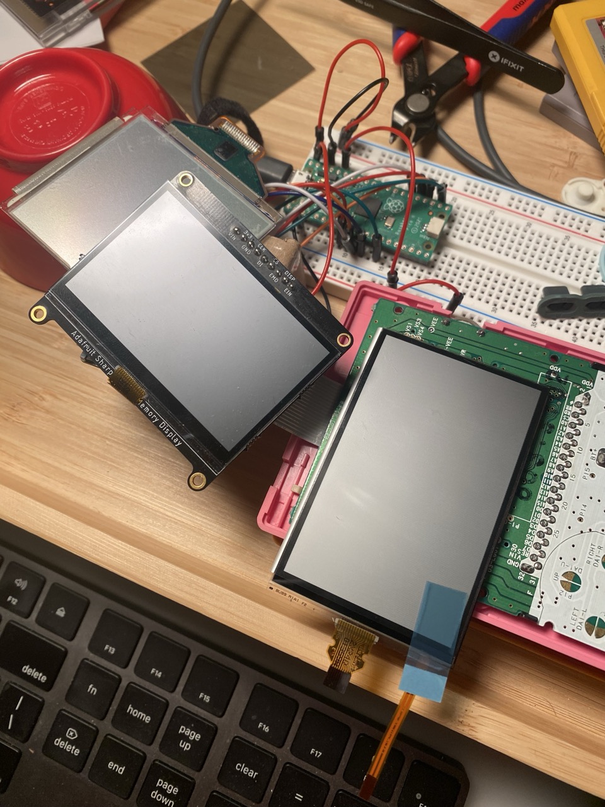
journey/img/IMG_9645 Large.jpeg
