bytendomods/RLCD-DMG/journey/img/IMG_9663 Large.jpeg

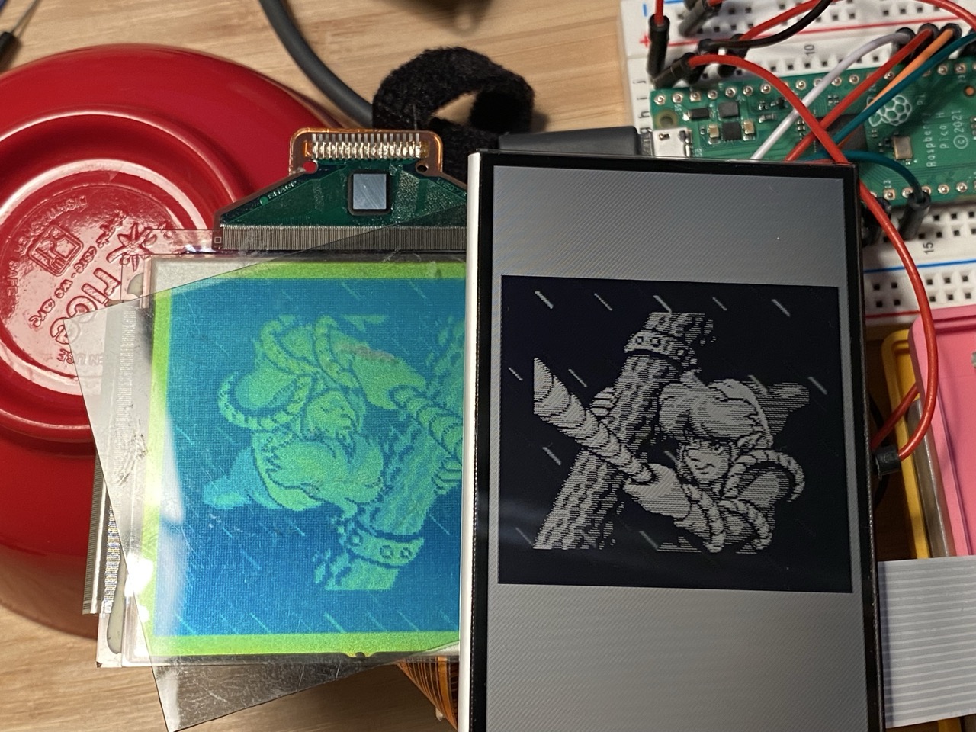
journey/img/IMG_9663 Large.jpeg
