bytendomods/RLCD-DMG/journey/img/IMG_9665 Large.jpeg

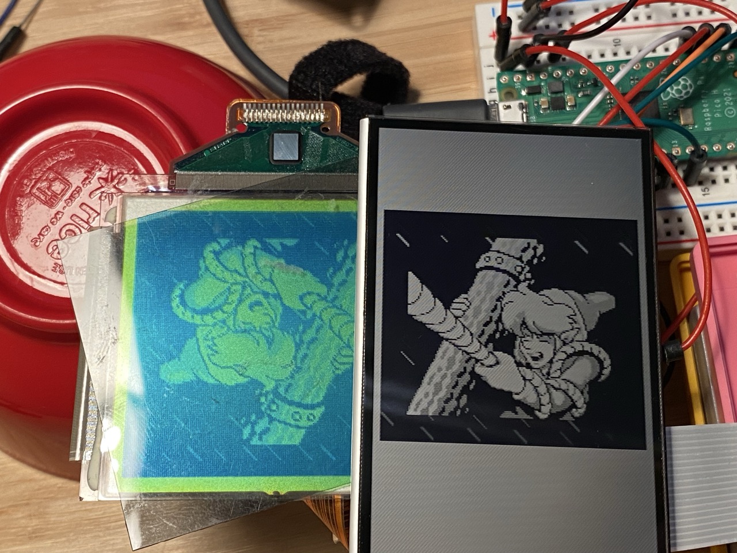
journey/img/IMG_9665 Large.jpeg
