bytendomods/RLCD-DMG/journey/img/IMG_9670 Large.jpeg

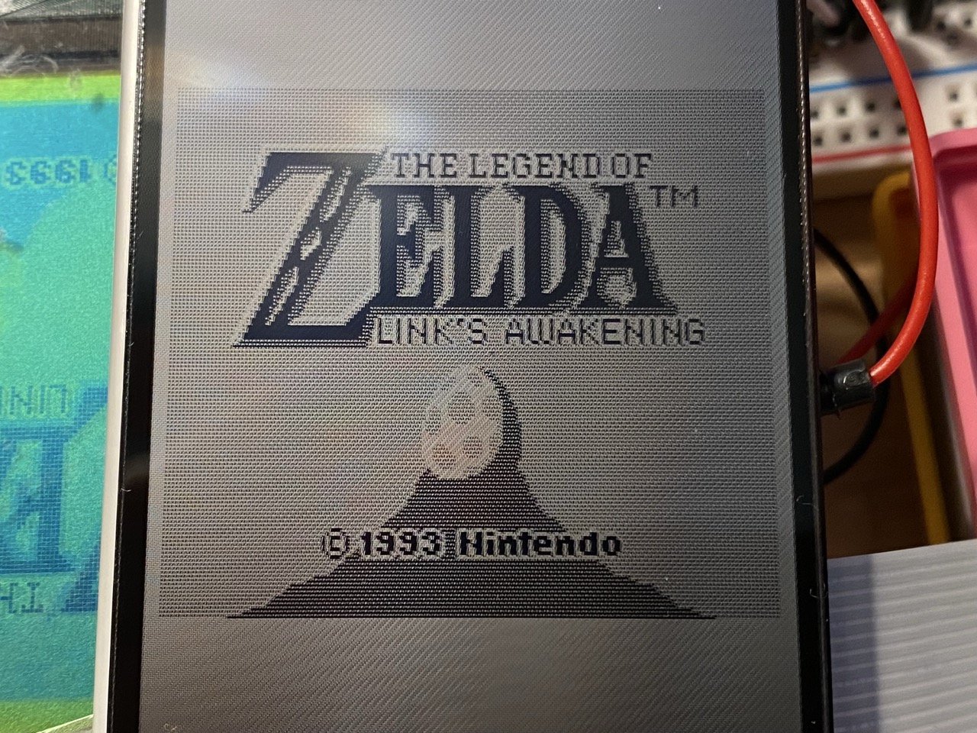
journey/img/IMG_9670 Large.jpeg
