bytendomods/RLCD-DMG/journey/img/IMG_9671 Large.jpeg

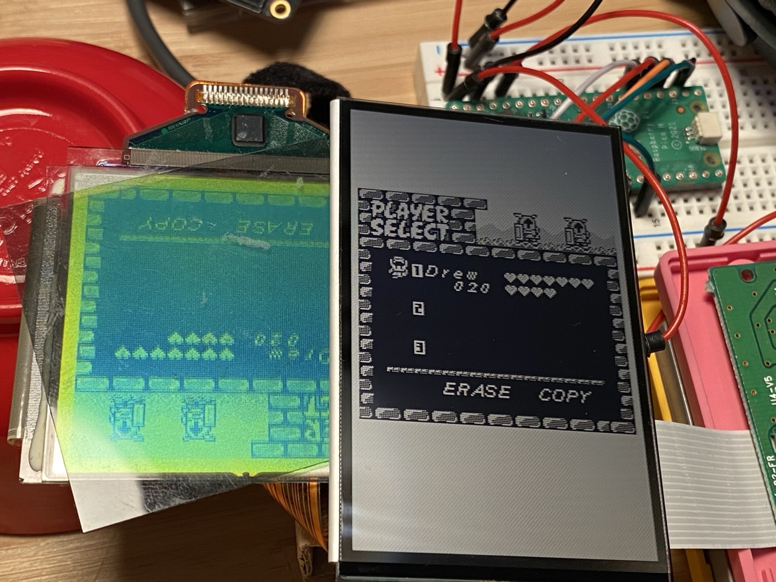
journey/img/IMG_9671 Large.jpeg
