bytendomods/RLCD-DMG/journey/img/IMG_9678 Large.jpeg

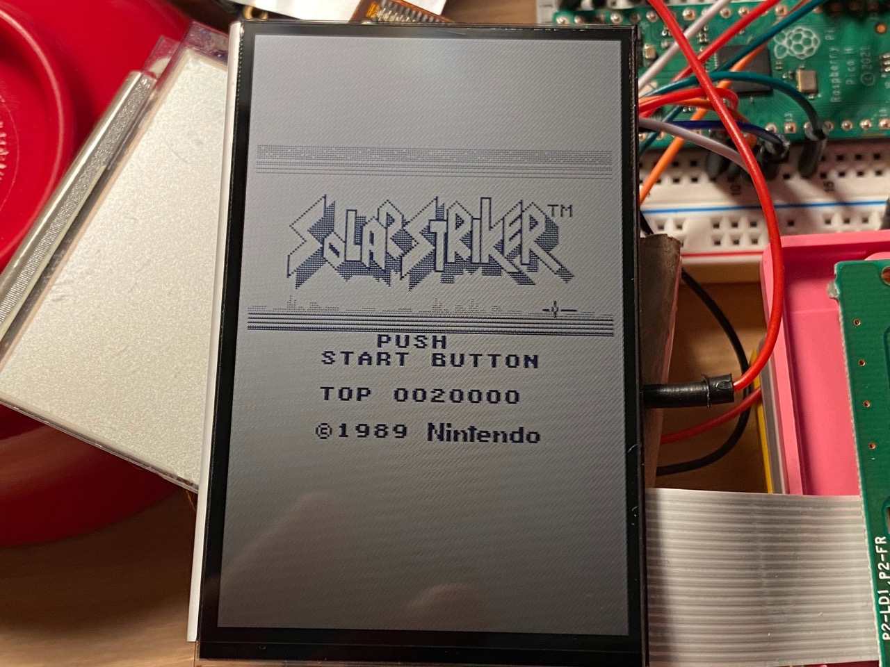
journey/img/IMG_9678 Large.jpeg
